Cade-Bray/Helgatchi/Hardware/Helgatchi front PCB/Components/801Logos/DC801.pdf

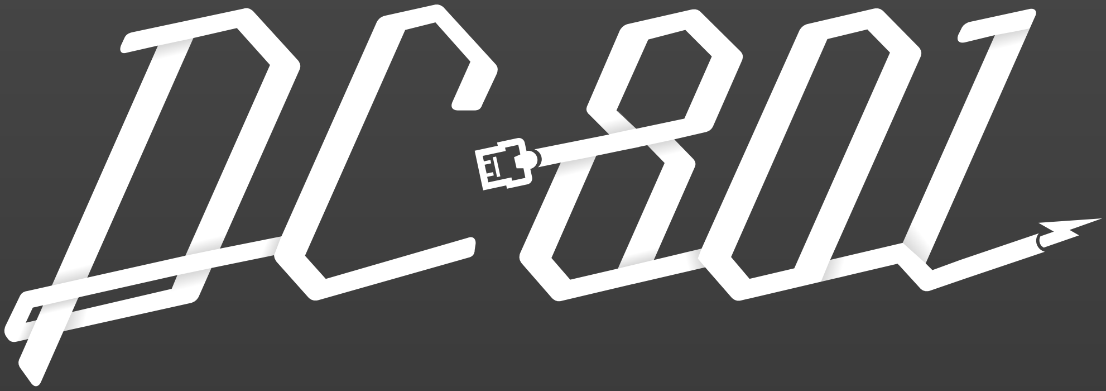
[picture p2: figure]
