Cade-Bray/Helgatchi/Hardware/Helgatchi front PCB/Components/801Logos/DC801_black.pdf

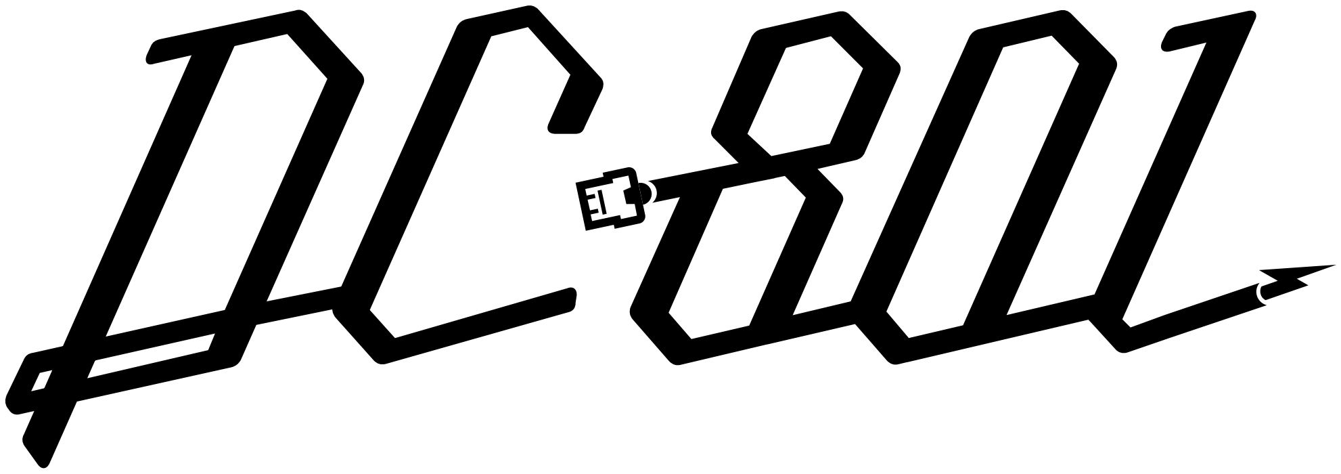
[picture p3: figure]
