Cade-Bray/Helgatchi/Hardware/Helgatchi front PCB/Components/801Logos/DC801_white.pdf

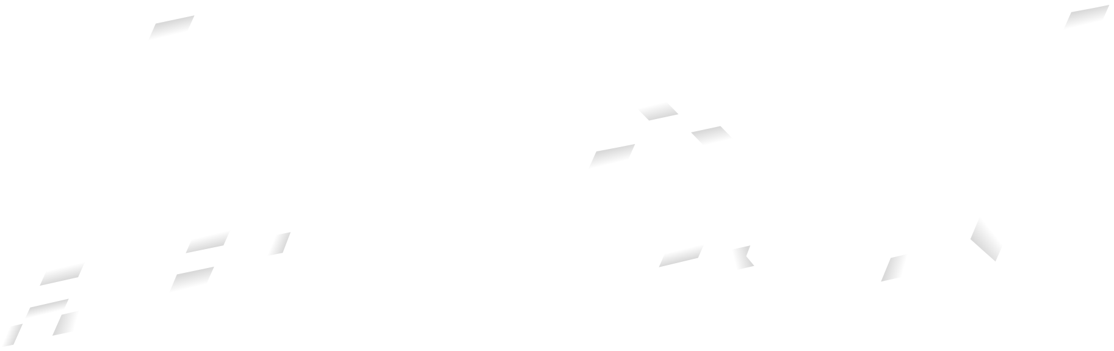
[picture p4: figure]
