Cade-Bray/Helgatchi/Hardware/Helgatchi Spacer/8.6mm Spacer antenna cutout 2.5mm holes.step

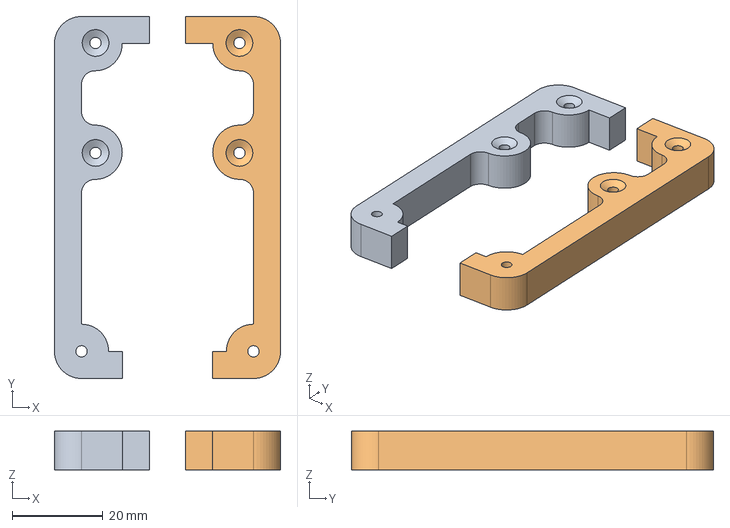
[picture p19: CAD file, 2026-04-04]
Hardware/Helgatchi Spacer/8.6mm Spacer antenna cutout 2.5mm holes.step
50.0 x 80.0 x 8.60 mm
