Cade-Bray/Helgatchi/Hardware/Helgatchi Spacer/Helgatchi Spacer - antenna - 2.5mm holes.dxf

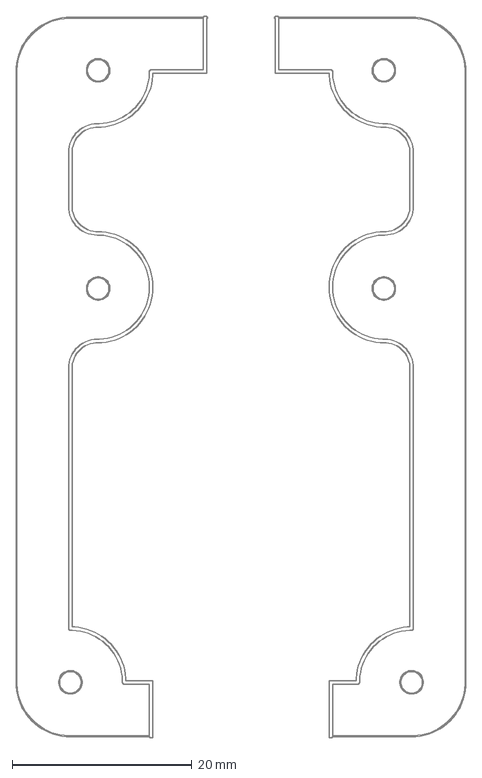
[picture p22: CAD file, 2026-04-04]
Hardware/Helgatchi Spacer/Helgatchi Spacer - antenna - 2.5mm holes.dxf
50.1 x 80.4 mm
