Cade-Bray/Helgatchi/Hardware/Helgatchi Spacer/Helgatchi spacer - antenna - 2.2mm holes.dxf

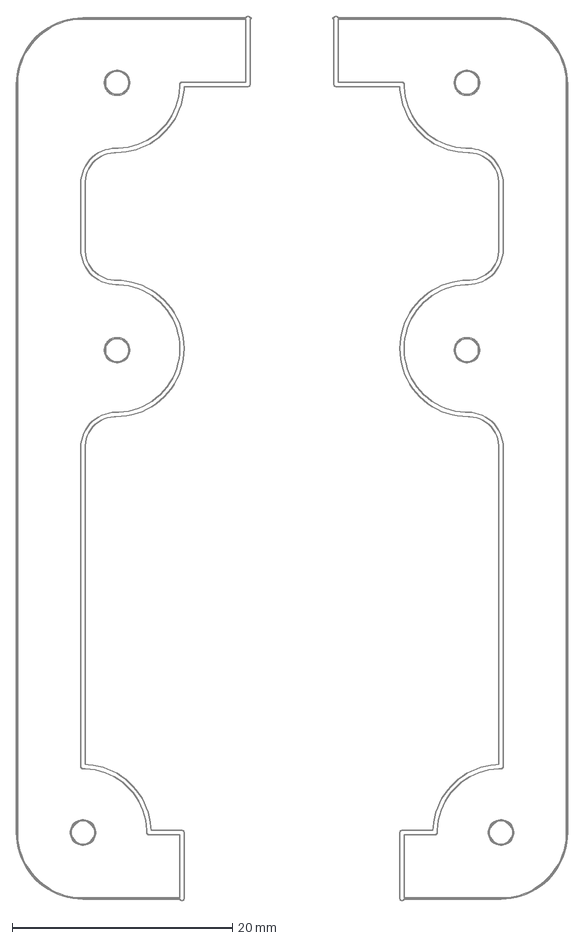
[picture p23: CAD file, 2026-04-04]
Hardware/Helgatchi Spacer/Helgatchi spacer - antenna - 2.2mm holes.dxf
50.1 x 80.4 mm
