Cade-Bray/Helgatchi/Hardware/Helgatchi Spacer/7.6mm Spacer.step

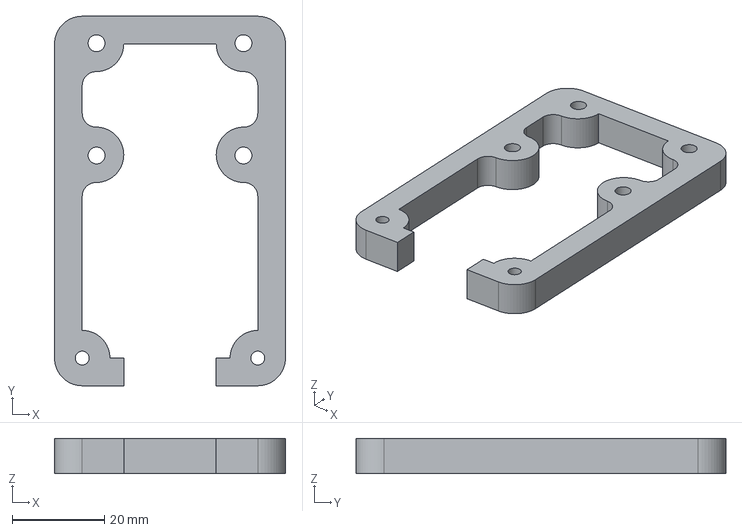
[picture p24: CAD file, 2026-03-17]
Hardware/Helgatchi Spacer/7.6mm Spacer.step
50.0 x 80.0 x 7.60 mm
