Cade-Bray/Helgatchi/Hardware/Helgatchi Spacer/8.6mm Spacer.step

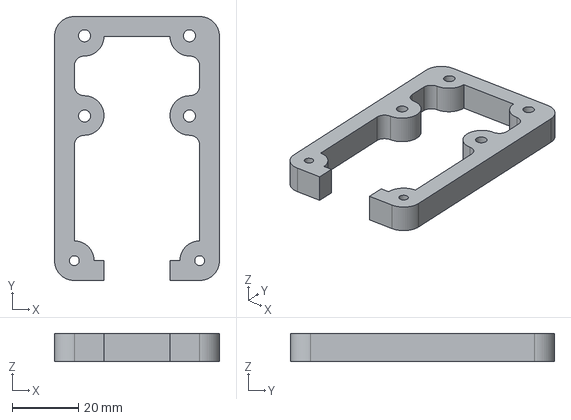
[picture p25: CAD file, 2026-03-17]
Hardware/Helgatchi Spacer/8.6mm Spacer.step
50.0 x 80.0 x 8.60 mm
