Cade-Bray/Helgatchi/Hardware/Helgatchi Spacer/Helgatchi back PCB-User_Drawings - unknown variant.dxf

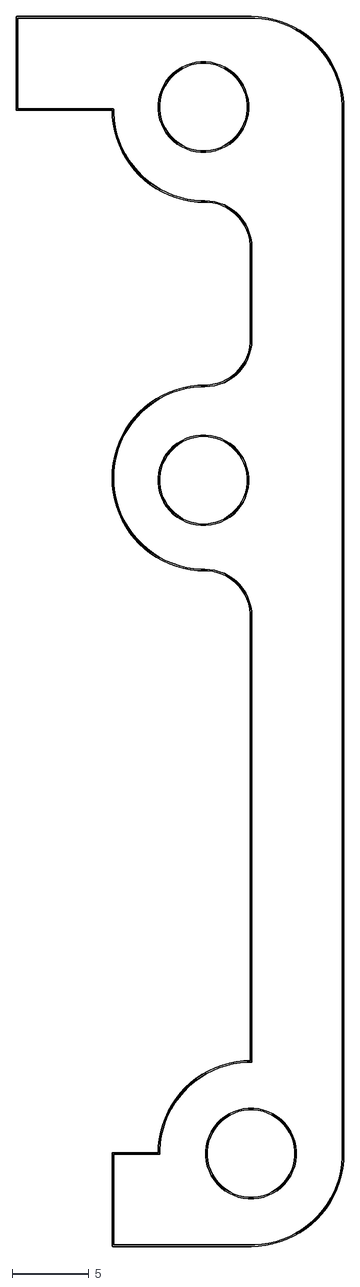
[picture p26: CAD file, 2026-02-06]
Hardware/Helgatchi Spacer/Helgatchi back PCB-User_Drawings - unknown variant.dxf
21.4 x 80.1
