Cade-Bray/Helgatchi/Hardware/Helgatchi Spacer/Helgatchi Spacer - antenna - standoffs.dxf

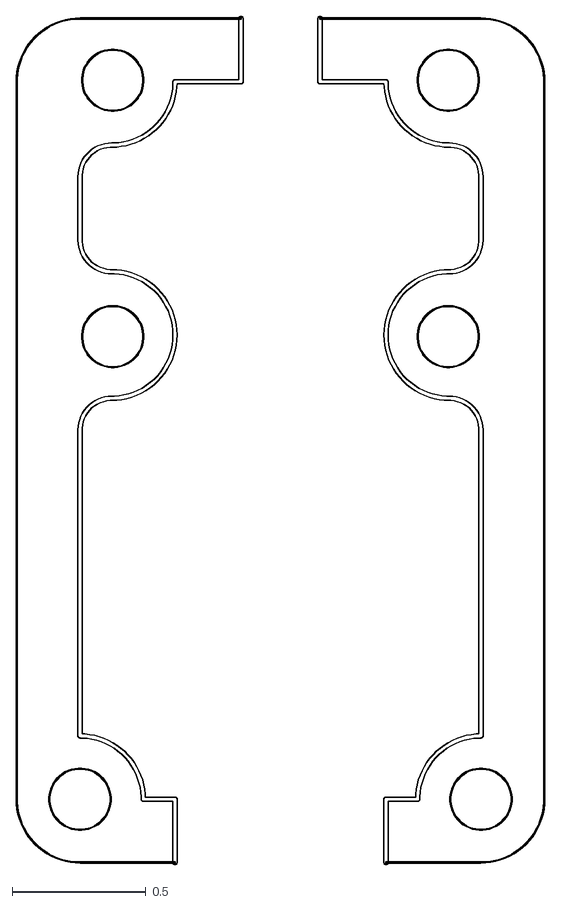
[picture p27: CAD file, 2026-02-05]
Hardware/Helgatchi Spacer/Helgatchi Spacer - antenna - standoffs.dxf
1.97 x 3.17
