Cade-Bray/Helgatchi/Hardware/Helgatchi Spacer/Helgatchi Spacer.dxf

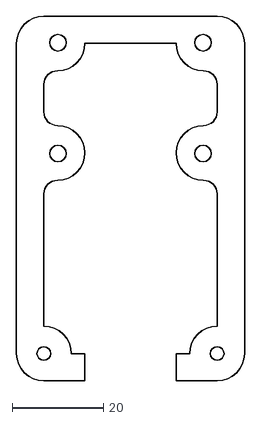
[picture p28: CAD file, 2026-01-26]
Hardware/Helgatchi Spacer/Helgatchi Spacer.dxf
50.0 x 80.0
