Cade-Bray/Helgatchi/Hardware/Helgatchi front PCB/Components/801Logos/801Labs_black.pdf

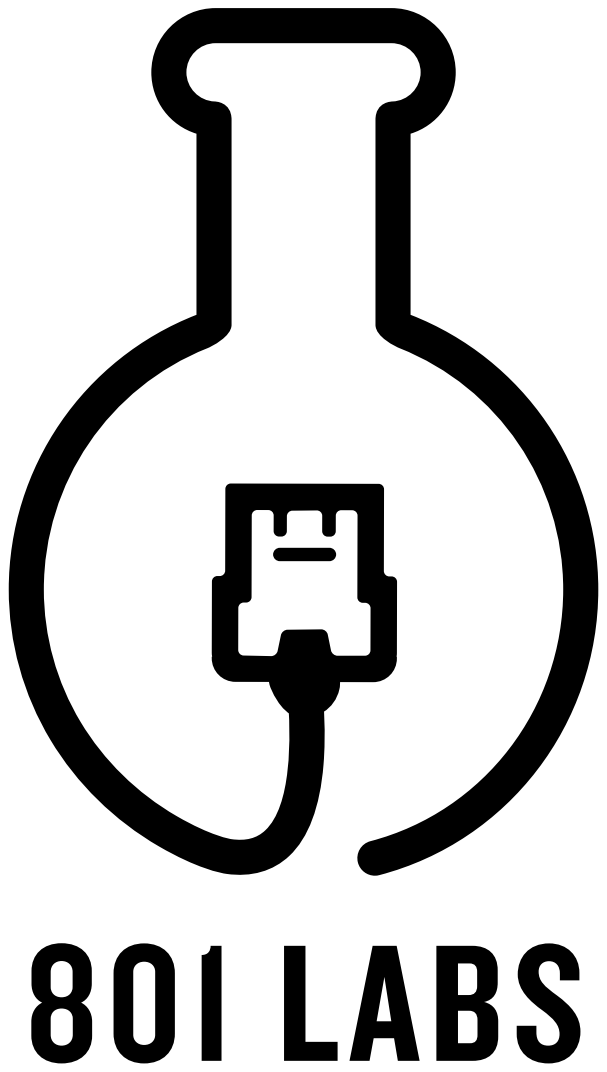
[picture p39: page 1]
