Cade-Bray/Helgatchi/Software/Helgatchi-Firmware/src/UI/ui.c

#include "ui.h"
#include "screens.h"
#include "images.h"
#include "actions.h"
#include "vars.h"

// ASSETS DEFINITION
const uint8_t assets[22956] = {
    0x7E, 0x45, 0x45, 0x5A, 0x03, 0x00, 0x06, 0x00, 0x00, 0x00, 0x00, 0x00, 0x24, 0x00, 0x00, 0x00,
    0x24, 0x00, 0x00, 0x00, 0x00, 0x00, 0x00, 0x00, 0x00, 0x00, 0x00, 0x00, 0x00, 0x00, 0x00, 0x00,
    0x00, 0x00, 0x00, 0x00, 0x20, 0x00, 0x00, 0x00, 0x00, 0x00, 0x00, 0x00, 0x00, 0x00, 0x00, 0x00,
    0x18, 0x01, 0xF0, 0x00, 0x03, 0x00, 0x00, 0x00, 0x24, 0x00, 0x00, 0x00, 0x02, 0x00, 0x00, 0x00,
    0x28, 0x00, 0x00, 0x00, 0x14, 0x00, 0x00, 0x00, 0x24, 0x00, 0x00, 0x00, 0x49, 0x00, 0x00, 0x00,
    0x70, 0x50, 0x00, 0x00, 0x02, 0x00, 0x00, 0x00, 0x64, 0x00, 0x00, 0x00, 0x68, 0x00, 0x00, 0x00,
    0x70, 0x00, 0x00, 0x00, 0x78, 0x00, 0x00, 0x00, 0x00, 0x00, 0xFF, 0xFF, 0x7C, 0x00, 0x00, 0x00,
    0xA8, 0x00, 0x00, 0x00, 0xD4, 0x00, 0x00, 0x00, 0x00, 0x01, 0x00, 0x00, 0x2C, 0x01, 0x00, 0x00,
    0x58, 0x01, 0x00, 0x00, 0x84, 0x01, 0x00, 0x00, 0xB0, 0x01, 0x00, 0x00, 0xDC, 0x01, 0x00, 0x00,
    0x08, 0x02, 0x00, 0x00, 0x34, 0x02, 0x00, 0x00, 0x60, 0x02, 0x00, 0x00, 0x8C, 0x02, 0x00, 0x00,
    0xB8, 0x02, 0x00, 0x00, 0xE4, 0x02, 0x00, 0x00, 0x10, 0x03, 0x00, 0x00, 0x3C, 0x03, 0x00, 0x00,
    0x68, 0x03, 0x00, 0x00, 0x94, 0x03, 0x00, 0x00, 0xC0, 0x03, 0x00, 0x00, 0xF0, 0x03, 0x00, 0x00,
    0xFC, 0x03, 0x00, 0x00, 0x08, 0x04, 0x00, 0x00, 0x06, 0x00, 0x00, 0x00, 0x08, 0x04, 0x00, 0x00,
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
    { NATIVE_VAR_TYPE_NONE, 0, 0 },
};

ActionExecFunc actions[] = {
    0
};

void ui_init() {
    eez_flow_init(assets, sizeof(assets), (lv_obj_t **)&objects, sizeof(objects), images, sizeof(images), actions);
}

void ui_tick() {
    eez_flow_tick();
    tick_screen(g_currentScreen);
}
