Cade-Bray/Helgatchi/Software/Helgatchi-Firmware/src/UI/screens.c

#include <string.h>

#include "screens.h"
#include "images.h"
#include "fonts.h"
#include "actions.h"
#include "vars.h"
#include "styles.h"
#include "ui.h"

#include <string.h>

objects_t objects;

static const char *screen_names[] = { "Main Menu", "Tutorial Splash Screen", "Tutorial", "Settings", "Info", "Screen Template", "Alerts", "Devices", "Device Updating", "Debug Info", "Overview", "Power Menu", "Power Action Screen", "Admin Menu", "Foxhunting Menu" };
static const char *object_names[] = { "main_menu", "tutorial_splash_screen", "tutorial", "settings", "info", "screen_template", "alerts", "devices", "device_updating", "debug_info", "overview", "power_menu", "power_action_screen", "admin_menu", "foxhunting_menu", "obj0", "obj0__top_bar", "obj0__left_text", "obj0__top_bar_center_text", "obj0__right_text", "settings_top_bar", "settings_top_bar__top_bar", "settings_top_bar__left_text", "settings_top_bar__top_bar_center_text", "settings_top_bar__right_text", "obj1", "obj1__top_bar", "obj1__left_text", "obj1__top_bar_center_text", "obj1__right_text", "obj2", "obj2__top_bar", "obj2__left_text", "obj2__top_bar_center_text", "obj2__right_text", "obj3", "obj3__main_content", "obj4", "obj4__top_bar", "obj4__left_text", "obj4__top_bar_center_text", "obj4__right_text", "obj5", "obj5__top_bar", "obj5__left_text", "obj5__top_bar_center_text", "obj5__right_text", "obj6", "obj6__top_bar", "obj6__left_text", "obj6__top_bar_center_text", "obj6__right_text", "obj7", "obj7__main_content", "obj8", "obj8__top_bar", "obj8__left_text", "obj8__top_bar_center_text", "obj8__right_text", "obj9", "obj9__top_bar", "obj9__left_text", "obj9__top_bar_center_text", "obj9__right_text", "obj10", "obj10__top_bar", "obj10__left_text", "obj10__top_bar_center_text", "obj10__right_text", "obj11", "obj11__top_bar", "obj11__left_text", "obj11__top_bar_center_text", "obj11__right_text", "obj12", "obj12__top_bar", "obj12__left_text", "obj12__top_bar_center_text", "obj12__right_text", "main_menu_scrolling_container", "overview_panel", "obj13", "devices_panel", "obj14", "alerts_panel", "games_panel", "settings_panel", "info_panel", "admin_panel", "obj15", "power_panel", "obj16", "obj17", "obj18", "obj19", "obj20", "splash_screen_tutorial", "obj21", "start_tutorial_button", "obj22", "obj23", "obj24", "end_tutorial_button", "obj25", "obj26", "obj27", "screen_brightness_dropdown", "led_brightness_dropdown", "vibrate_on_alert_switch", "le_ds_on_alert_switch", "wake_screen_on_alert_switch", "obj28", "focus_on_alert_page_switch", "ble_scanning_switch", "active_ble_scanning", "ignore_nameless_random_ma_cs", "wi_fi_scanning_switch", "scan_mode_dropdown", "debug_over_serial_switch", "debug_level_dropdown", "sleep_with_serial_switch", "sleep_with_usb_switch", "sleep_while_charging", "debug_screen_label", "debug_screen_button", "sleep_timer_label", "sleep_button", "reboot_button", "shipping_mode_button", "restart_tutorial_button", "obj29", "obj30", "obj31", "obj32", "obj33", "obj34", "obj35", "obj36", "obj37", "device_info", "version_info", "hardware_specs_container", "software_specs_container", "credits_container", "obj38", "alert_container", "no_alerts_label", "devices_container", "obj39", "system___health_container", "power_container", "scanning_container", "rules___alerts_container", "helga", "sleep_now_button", "sleep_countdown_text", "restart_button", "power_off_", "obj40", "obj41", "obj42", "power_action_text", "admin_command_container", "admin_command_dropdown", "admin_message_container", "admin_message_dropdown", "admin_led_pattern_container", "admin_led_mode_dropdown", "admin_duration_container", "admin_duration_dropdown", "admin_command_button", "admin_command_button_label", "signal_quality", "device_name", "last_seen", "device_rssi", "device_details", "obj43", "obj44", "obj45", "obj46", "obj47", "obj48", "obj49", "obj50", "obj51", "obj52", "obj53", "obj54", "obj55" };

//
// Event handlers
//

lv_obj_t *tick_value_change_obj;

static void event_handler_cb_main_menu_main_menu(lv_event_t *e) {
    lv_event_code_t event = lv_event_get_code(e);
    void *flowState = lv_event_get_user_data(e);
    (void)flowState;
    
    if (event == LV_EVENT_SCREEN_LOAD_START) {
        // group: UINavigation
        lv_group_remove_all_objs(groups.UINavigation);
        lv_group_add_obj(groups.UINavigation, objects.overview_panel);
        lv_group_add_obj(groups.UINavigation, objects.devices_panel);
        lv_group_add_obj(groups.UINavigation, objects.alerts_panel);
        lv_group_add_obj(groups.UINavigation, objects.games_panel);
        lv_group_add_obj(groups.UINavigation, objects.settings_panel);
        lv_group_add_obj(groups.UINavigation, objects.info_panel);
        lv_group_add_obj(groups.UINavigation, objects.admin_panel);
        lv_group_add_obj(groups.UINavigation, objects.power_panel);
    }
    if (event == LV_EVENT_SCREEN_LOADED) {
        e->user_data = (void *)0;
        flowPropagateValueLVGLEvent(flowState, 1, 0, e);
    }
}

static void event_handler_cb_main_menu_overview_panel(lv_event_t *e) {
    lv_event_code_t event = lv_event_get_code(e);
    void *flowState = lv_event_get_user_data(e);
    (void)flowState;
    
    if (event == LV_EVENT_CLICKED) {
        e->user_data = (void *)0;
        flowPropagateValueLVGLEvent(flowState, 3, 0, e);
    }
}

static void event_handler_cb_main_menu_devices_panel(lv_event_t *e) {
    lv_event_code_t event = lv_event_get_code(e);
    void *flowState = lv_event_get_user_data(e);
    (void)flowState;
    
    if (event == LV_EVENT_CLICKED) {
        e->user_data = (void *)0;
        flowPropagateValueLVGLEvent(flowState, 7, 0, e);
    }
}

static void event_handler_cb_main_menu_alerts_panel(lv_event_t *e) {
    lv_event_code_t event = lv_event_get_code(e);
    void *flowState = lv_event_get_user_data(e);
    (void)flowState;
    
    if (event == LV_EVENT_CLICKED) {
        e->user_data = (void *)0;
        flowPropagateValueLVGLEvent(flowState, 11, 0, e);
    }
}

static void event_handler_cb_main_menu_games_panel(lv_event_t *e) {
    lv_event_code_t event = lv_event_get_code(e);
    void *flowState = lv_event_get_user_data(e);
    (void)flowState;
    
    if (event == LV_EVENT_CLICKED) {
        e->user_data = (void *)0;
        flowPropagateValueLVGLEvent(flowState, 15, 0, e);
    }
}

static void event_handler_cb_main_menu_settings_panel(lv_event_t *e) {
    lv_event_code_t event = lv_event_get_code(e);
    void *flowState = lv_event_get_user_data(e);
    (void)flowState;
    
    if (event == LV_EVENT_CLICKED) {
        e->user_data = (void *)0;
        flowPropagateValueLVGLEvent(flowState, 19, 0, e);
    }
}

static void event_handler_cb_main_menu_info_panel(lv_event_t *e) {
    lv_event_code_t event = lv_event_get_code(e);
    void *flowState = lv_event_get_user_data(e);
    (void)flowState;
    
    if (event == LV_EVENT_CLICKED) {
        e->user_data = (void *)0;
        flowPropagateValueLVGLEvent(flowState, 23, 0, e);
    }
}

static void event_handler_cb_main_menu_admin_panel(lv_event_t *e) {
    lv_event_code_t event = lv_event_get_code(e);
    void *flowState = lv_event_get_user_data(e);
    (void)flowState;
    
    if (event == LV_EVENT_CLICKED) {
        e->user_data = (void *)0;
        flowPropagateValueLVGLEvent(flowState, 27, 0, e);
    }
}

static void event_handler_cb_main_menu_power_panel(lv_event_t *e) {
    lv_event_code_t event = lv_event_get_code(e);
    void *flowState = lv_event_get_user_data(e);
    (void)flowState;
    
    if (event == LV_EVENT_CLICKED) {
        e->user_data = (void *)0;
        flowPropagateValueLVGLEvent(flowState, 31, 0, e);
    }
}

static void event_handler_cb_tutorial_splash_screen_tutorial_splash_screen(lv_event_t *e) {
    lv_event_code_t event = lv_event_get_code(e);
    void *flowState = lv_event_get_user_data(e);
    (void)flowState;
    
    if (event == LV_EVENT_SCREEN_LOAD_START) {
        // group: UINavigation
        lv_group_remove_all_objs(groups.UINavigation);
        lv_group_add_obj(groups.UINavigation, objects.start_tutorial_button);
    }
}

static void event_handler_cb_tutorial_splash_screen_start_tutorial_button(lv_event_t *e) {
    lv_event_code_t event = lv_event_get_code(e);
    void *flowState = lv_event_get_user_data(e);
    (void)flowState;
    
    if (event == LV_EVENT_CLICKED) {
        e->user_data = (void *)0;
        flowPropagateValueLVGLEvent(flowState, 4, 0, e);
    }
}

static void event_handler_cb_tutorial_tutorial(lv_event_t *e) {
    lv_event_code_t event = lv_event_get_code(e);
    void *flowState = lv_event_get_user_data(e);
    (void)flowState;
    
    if (event == LV_EVENT_SCREEN_LOAD_START) {
        // group: UINavigation
        lv_group_remove_all_objs(groups.UINavigation);
        lv_group_add_obj(groups.UINavigation, objects.obj43);
        lv_group_add_obj(groups.UINavigation, objects.obj44);
        lv_group_add_obj(groups.UINavigation, objects.obj45);
        lv_group_add_obj(groups.UINavigation, objects.obj46);
        lv_group_add_obj(groups.UINavigation, objects.obj47);
        lv_group_add_obj(groups.UINavigation, objects.end_tutorial_button);
    }
    if (event == LV_EVENT_SCREEN_LOADED) {
        e->user_data = (void *)0;
        flowPropagateValueLVGLEvent(flowState, 1, 0, e);
    }
    if (event == LV_EVENT_SCREEN_UNLOADED) {
        e->user_data = (void *)0;
        flowPropagateValueLVGLEvent(flowState, 1, 1, e);
    }
}

static void event_handler_cb_tutorial_end_tutorial_button(lv_event_t *e) {
    lv_event_code_t event = lv_event_get_code(e);
    void *flowState = lv_event_get_user_data(e);
    (void)flowState;
    
    if (event == LV_EVENT_CLICKED) {
        e->user_data = (void *)0;
        flowPropagateValueLVGLEvent(flowState, 21, 0, e);
    }
}

static void event_handler_cb_settings_settings(lv_event_t *e) {
    lv_event_code_t event = lv_event_get_code(e);
    void *flowState = lv_event_get_user_data(e);
    (void)flowState;
    
    if (event == LV_EVENT_SCREEN_LOAD_START) {
        // group: UINavigation
        lv_group_remove_all_objs(groups.UINavigation);
        lv_group_add_obj(groups.UINavigation, objects.screen_brightness_dropdown);
        lv_group_add_obj(groups.UINavigation, objects.led_brightness_dropdown);
        lv_group_add_obj(groups.UINavigation, objects.vibrate_on_alert_switch);
        lv_group_add_obj(groups.UINavigation, objects.le_ds_on_alert_switch);
        lv_group_add_obj(groups.UINavigation, objects.wake_screen_on_alert_switch);
        lv_group_add_obj(groups.UINavigation, objects.focus_on_alert_page_switch);
        lv_group_add_obj(groups.UINavigation, objects.ble_scanning_switch);
        lv_group_add_obj(groups.UINavigation, objects.active_ble_scanning);
        lv_group_add_obj(groups.UINavigation, objects.ignore_nameless_random_ma_cs);
        lv_group_add_obj(groups.UINavigation, objects.wi_fi_scanning_switch);
        lv_group_add_obj(groups.UINavigation, objects.scan_mode_dropdown);
        lv_group_add_obj(groups.UINavigation, objects.debug_over_serial_switch);
        lv_group_add_obj(groups.UINavigation, objects.debug_level_dropdown);
        lv_group_add_obj(groups.UINavigation, objects.sleep_with_serial_switch);
        lv_group_add_obj(groups.UINavigation, objects.sleep_with_usb_switch);
        lv_group_add_obj(groups.UINavigation, objects.sleep_while_charging);
        lv_group_add_obj(groups.UINavigation, objects.debug_screen_button);
        lv_group_add_obj(groups.UINavigation, objects.sleep_button);
        lv_group_add_obj(groups.UINavigation, objects.reboot_button);
        lv_group_add_obj(groups.UINavigation, objects.shipping_mode_button);
        lv_group_add_obj(groups.UINavigation, objects.restart_tutorial_button);
    }
}

static void event_handler_cb_settings_wake_screen_on_alert_switch(lv_event_t *e) {
    lv_event_code_t event = lv_event_get_code(e);
    void *flowState = lv_event_get_user_data(e);
    (void)flowState;
    
    if (event == LV_EVENT_VALUE_CHANGED) {
        if (!lv_obj_has_state(lv_event_get_target_obj(e), LV_STATE_CHECKED)) {
            e->user_data = (void *)0;
            flowPropagateValueLVGLEvent(flowState, 19, 0, e);
        }
    }
    if (event == LV_EVENT_VALUE_CHANGED) {
        if (lv_obj_has_state(lv_event_get_target_obj(e), LV_STATE_CHECKED)) {
            e->user_data = (void *)0;
            flowPropagateValueLVGLEvent(flowState, 19, 1, e);
        }
    }
}

static void event_handler_cb_settings_debug_screen_button(lv_event_t *e) {
    lv_event_code_t event = lv_event_get_code(e);
    void *flowState = lv_event_get_user_data(e);
    (void)flowState;
    
    if (event == LV_EVENT_CLICKED) {
        e->user_data = (void *)0;
        flowPropagateValueLVGLEvent(flowState, 57, 0, e);
    }
}

static void event_handler_cb_settings_restart_tutorial_button(lv_event_t *e) {
    lv_event_code_t event = lv_event_get_code(e);
    void *flowState = lv_event_get_user_data(e);
    (void)flowState;
    
    if (event == LV_EVENT_CLICKED) {
        e->user_data = (void *)0;
        flowPropagateValueLVGLEvent(flowState, 73, 0, e);
    }
}

static void event_handler_cb_info_info(lv_event_t *e) {
    lv_event_code_t event = lv_event_get_code(e);
    void *flowState = lv_event_get_user_data(e);
    (void)flowState;
    
    if (event == LV_EVENT_SCREEN_LOAD_START) {
        // group: UINavigation
        lv_group_remove_all_objs(groups.UINavigation);
        lv_group_add_obj(groups.UINavigation, objects.obj48);
        lv_group_add_obj(groups.UINavigation, objects.obj49);
        lv_group_add_obj(groups.UINavigation, objects.obj50);
        lv_group_add_obj(groups.UINavigation, objects.obj51);
    }
}

static void event_handler_cb_screen_template_screen_template(lv_event_t *e) {
    lv_event_code_t event = lv_event_get_code(e);
    void *flowState = lv_event_get_user_data(e);
    (void)flowState;
    
    if (event == LV_EVENT_SCREEN_LOAD_START) {
        // group: UINavigation
        lv_group_remove_all_objs(groups.UINavigation);
    }
}

static void event_handler_cb_alerts_alerts(lv_event_t *e) {
    lv_event_code_t event = lv_event_get_code(e);
    void *flowState = lv_event_get_user_data(e);
    (void)flowState;
    
    if (event == LV_EVENT_SCREEN_LOAD_START) {
        // group: UINavigation
        lv_group_remove_all_objs(groups.UINavigation);
    }
}

static void event_handler_cb_devices_devices(lv_event_t *e) {
    lv_event_code_t event = lv_event_get_code(e);
    void *flowState = lv_event_get_user_data(e);
    (void)flowState;
    
    if (event == LV_EVENT_SCREEN_LOAD_START) {
        // group: UINavigation
        lv_group_remove_all_objs(groups.UINavigation);
    }
}

static void event_handler_cb_device_updating_device_updating(lv_event_t *e) {
    lv_event_code_t event = lv_event_get_code(e);
    void *flowState = lv_event_get_user_data(e);
    (void)flowState;
    
    if (event == LV_EVENT_SCREEN_LOAD_START) {
        // group: UINavigation
        lv_group_remove_all_objs(groups.UINavigation);
    }
}

static void event_handler_cb_debug_info_debug_info(lv_event_t *e) {
    lv_event_code_t event = lv_event_get_code(e);
    void *flowState = lv_event_get_user_data(e);
    (void)flowState;
    
    if (event == LV_EVENT_SCREEN_LOAD_START) {
        // group: UINavigation
        lv_group_remove_all_objs(groups.UINavigation);
        lv_group_add_obj(groups.UINavigation, objects.obj52);
        lv_group_add_obj(groups.UINavigation, objects.obj53);
        lv_group_add_obj(groups.UINavigation, objects.obj54);
        lv_group_add_obj(groups.UINavigation, objects.obj55);
    }
}

static void event_handler_cb_overview_overview(lv_event_t *e) {
    lv_event_code_t event = lv_event_get_code(e);
    void *flowState = lv_event_get_user_data(e);
    (void)flowState;
    
    if (event == LV_EVENT_SCREEN_LOAD_START) {
        // group: UINavigation
        lv_group_remove_all_objs(groups.UINavigation);
    }
}

static void event_handler_cb_power_menu_power_menu(lv_event_t *e) {
    lv_event_code_t event = lv_event_get_code(e);
    void *flowState = lv_event_get_user_data(e);
    (void)flowState;
    
    if (event == LV_EVENT_SCREEN_LOAD_START) {
        // group: UINavigation
        lv_group_remove_all_objs(groups.UINavigation);
        lv_group_add_obj(groups.UINavigation, objects.sleep_now_button);
        lv_group_add_obj(groups.UINavigation, objects.restart_button);
        lv_group_add_obj(groups.UINavigation, objects.power_off_);
    }
}

static void event_handler_cb_power_action_screen_power_action_screen(lv_event_t *e) {
    lv_event_code_t event = lv_event_get_code(e);
    void *flowState = lv_event_get_user_data(e);
    (void)flowState;
    
    if (event == LV_EVENT_SCREEN_LOAD_START) {
        // group: UINavigation
        lv_group_remove_all_objs(groups.UINavigation);
    }
}

static void event_handler_cb_admin_menu_admin_menu(lv_event_t *e) {
    lv_event_code_t event = lv_event_get_code(e);
    void *flowState = lv_event_get_user_data(e);
    (void)flowState;
    
    if (event == LV_EVENT_SCREEN_LOAD_START) {
        // group: UINavigation
        lv_group_remove_all_objs(groups.UINavigation);
        lv_group_add_obj(groups.UINavigation, objects.admin_command_dropdown);
        lv_group_add_obj(groups.UINavigation, objects.admin_message_dropdown);
        lv_group_add_obj(groups.UINavigation, objects.admin_led_mode_dropdown);
        lv_group_add_obj(groups.UINavigation, objects.admin_duration_dropdown);
    }
}

static void event_handler_cb_foxhunting_menu_foxhunting_menu(lv_event_t *e) {
    lv_event_code_t event = lv_event_get_code(e);
    void *flowState = lv_event_get_user_data(e);
    (void)flowState;
    
    if (event == LV_EVENT_SCREEN_LOAD_START) {
        // group: UINavigation
        lv_group_remove_all_objs(groups.UINavigation);
    }
}

//
// Screens
//

void create_screen_main_menu() {
    void *flowState = getFlowState(0, 0);
    (void)flowState;
    lv_obj_t *obj = lv_obj_create(0);
    objects.main_menu = obj;
    lv_obj_set_pos(obj, 0, 0);
    lv_obj_set_size(obj, 280, 240);
    lv_obj_add_event_cb(obj, event_handler_cb_main_menu_main_menu, LV_EVENT_ALL, flowState);
    {
        lv_obj_t *parent_obj = obj;
        {
            lv_obj_t *obj = lv_obj_create(parent_obj);
            objects.obj0 = obj;
            lv_obj_set_pos(obj, 0, 0);
            lv_obj_set_size(obj, 280, 36);
            lv_obj_set_style_pad_left(obj, 0, LV_PART_MAIN | LV_STATE_DEFAULT);
            lv_obj_set_style_pad_top(obj, 0, LV_PART_MAIN | LV_STATE_DEFAULT);
            lv_obj_set_style_pad_right(obj, 0, LV_PART_MAIN | LV_STATE_DEFAULT);
            lv_obj_set_style_pad_bottom(obj, 0, LV_PART_MAIN | LV_STATE_DEFAULT);
            lv_obj_set_style_bg_opa(obj, 0, LV_PART_MAIN | LV_STATE_DEFAULT);
            lv_obj_set_style_border_width(obj, 0, LV_PART_MAIN | LV_STATE_DEFAULT);
            create_user_widget_top_bar(obj, getFlowState(flowState, 0), 16);
            lv_obj_add_flag(obj, LV_OBJ_FLAG_FLOATING);
        }
        {
            // Main Menu Scrolling Container
            lv_obj_t *obj = lv_obj_create(parent_obj);
            objects.main_menu_scrolling_container = obj;
            lv_obj_set_pos(obj, 0, 0);
            lv_obj_set_size(obj, LV_PCT(100), LV_PCT(85));
            lv_obj_set_style_pad_left(obj, 0, LV_PART_MAIN | LV_STATE_DEFAULT);
            lv_obj_set_style_pad_top(obj, 0, LV_PART_MAIN | LV_STATE_DEFAULT);
            lv_obj_set_style_pad_right(obj, 0, LV_PART_MAIN | LV_STATE_DEFAULT);
            lv_obj_set_style_pad_bottom(obj, 0, LV_PART_MAIN | LV_STATE_DEFAULT);
            lv_obj_set_style_bg_opa(obj, 0, LV_PART_MAIN | LV_STATE_DEFAULT);
            lv_obj_set_style_border_width(obj, 0, LV_PART_MAIN | LV_STATE_DEFAULT);
            lv_obj_set_style_radius(obj, 0, LV_PART_MAIN | LV_STATE_DEFAULT);
            lv_obj_add_flag(obj, LV_OBJ_FLAG_SCROLL_ON_FOCUS|LV_OBJ_FLAG_SCROLL_ONE);
            lv_obj_remove_flag(obj, LV_OBJ_FLAG_CLICKABLE|LV_OBJ_FLAG_SCROLL_MOMENTUM);
            lv_obj_set_scrollbar_mode(obj, LV_SCROLLBAR_MODE_ON);
            lv_obj_set_scroll_dir(obj, LV_DIR_HOR);
            lv_obj_set_scroll_snap_x(obj, LV_SCROLL_SNAP_CENTER);
            lv_obj_set_style_align(obj, LV_ALIGN_BOTTOM_MID, LV_PART_MAIN | LV_STATE_DEFAULT);
            lv_obj_set_style_layout(obj, LV_LAYOUT_FLEX, LV_PART_MAIN | LV_STATE_DEFAULT);
            lv_obj_set_style_flex_flow(obj, LV_FLEX_FLOW_COLUMN_WRAP, LV_PART_MAIN | LV_STATE_DEFAULT);
            {
                lv_obj_t *parent_obj = obj;
                {
                    // Overview Panel
                    lv_obj_t *obj = lv_obj_create(parent_obj);
                    objects.overview_panel = obj;
                    lv_obj_set_pos(obj, 14, 28);
                    lv_obj_set_size(obj, LV_PCT(100), LV_PCT(100));
                    lv_obj_add_event_cb(obj, event_handler_cb_main_menu_overview_panel, LV_EVENT_ALL, flowState);
                    lv_obj_add_flag(obj, LV_OBJ_FLAG_SCROLL_ON_FOCUS);
                    lv_obj_add_state(obj, LV_STATE_FOCUS_KEY);
                    add_style_default_main_menu_panel(obj);
                    {
                        lv_obj_t *parent_obj = obj;
                        {
                            lv_obj_t *obj = lv_label_create(parent_obj);
                            objects.obj13 = obj;
                            lv_obj_set_pos(obj, 0, 0);
                            lv_obj_set_size(obj, LV_SIZE_CONTENT, LV_SIZE_CONTENT);
                            lv_obj_set_style_text_font(obj, &lv_font_montserrat_44, LV_PART_MAIN | LV_STATE_DEFAULT);
                            lv_obj_set_style_text_color(obj, lv_color_hex(0xfafafa), LV_PART_MAIN | LV_STATE_DEFAULT);
                            lv_label_set_text(obj, "");
                        }
                        {
                            lv_obj_t *obj = lv_label_create(parent_obj);
                            lv_obj_set_pos(obj, 0, 0);
                            lv_obj_set_size(obj, LV_SIZE_CONTENT, LV_SIZE_CONTENT);
                            lv_obj_set_style_text_font(obj, &lv_font_montserrat_22, LV_PART_MAIN | LV_STATE_DEFAULT);
                            lv_label_set_text(obj, _("Status"));
                        }
                        {
                            lv_obj_t *obj = lv_label_create(parent_obj);
                            lv_obj_set_pos(obj, 0, 0);
                            lv_obj_set_size(obj, LV_PCT(90), LV_SIZE_CONTENT);
                            lv_obj_set_style_text_align(obj, LV_TEXT_ALIGN_CENTER, LV_PART_MAIN | LV_STATE_DEFAULT);
                            lv_label_set_text_static(obj, "Helga will show you what she's doing!");
                        }
                    }
                }
                {
                    // Devices Panel
                    lv_obj_t *obj = lv_obj_create(parent_obj);
                    objects.devices_panel = obj;
                    lv_obj_set_pos(obj, 14, 28);
                    lv_obj_set_size(obj, LV_PCT(100), LV_PCT(100));
                    lv_obj_add_event_cb(obj, event_handler_cb_main_menu_devices_panel, LV_EVENT_ALL, flowState);
                    lv_obj_add_flag(obj, LV_OBJ_FLAG_SCROLL_ON_FOCUS);
                    lv_obj_add_state(obj, LV_STATE_FOCUS_KEY);
                    add_style_default_main_menu_panel(obj);
                    {
                        lv_obj_t *parent_obj = obj;
                        {
                            lv_obj_t *obj = lv_label_create(parent_obj);
                            objects.obj14 = obj;
                            lv_obj_set_pos(obj, 0, 0);
                            lv_obj_set_size(obj, LV_SIZE_CONTENT, LV_SIZE_CONTENT);
                            lv_obj_set_style_text_font(obj, &lv_font_montserrat_44, LV_PART_MAIN | LV_STATE_DEFAULT);
                            lv_obj_set_style_text_color(obj, lv_color_hex(0xfafafa), LV_PART_MAIN | LV_STATE_DEFAULT);
                            lv_label_set_text(obj, "");
                        }
                        {
                            lv_obj_t *obj = lv_label_create(parent_obj);
                            lv_obj_set_pos(obj, 0, 0);
                            lv_obj_set_size(obj, LV_SIZE_CONTENT, LV_SIZE_CONTENT);
                            lv_obj_set_style_text_font(obj, &lv_font_montserrat_22, LV_PART_MAIN | LV_STATE_DEFAULT);
                            lv_label_set_text(obj, _("Devices"));
                        }
                        {
                            lv_obj_t *obj = lv_label_create(parent_obj);
                            lv_obj_set_pos(obj, 0, 0);
                            lv_obj_set_size(obj, LV_SIZE_CONTENT, LV_SIZE_CONTENT);
                            lv_label_set_text_static(obj, "View scan results!");
                        }
                    }
                }
                {
                    // Alerts Panel
                    lv_obj_t *obj = lv_obj_create(parent_obj);
                    objects.alerts_panel = obj;
                    lv_obj_set_pos(obj, 14, 28);
                    lv_obj_set_size(obj, LV_PCT(100), LV_PCT(100));
                    lv_obj_add_event_cb(obj, event_handler_cb_main_menu_alerts_panel, LV_EVENT_ALL, flowState);
                    lv_obj_add_flag(obj, LV_OBJ_FLAG_SCROLL_ON_FOCUS);
                    add_style_default_main_menu_panel(obj);
                    {
                        lv_obj_t *parent_obj = obj;
                        {
                            lv_obj_t *obj = lv_label_create(parent_obj);
                            objects.obj16 = obj;
                            lv_obj_set_pos(obj, 0, 0);
                            lv_obj_set_size(obj, LV_SIZE_CONTENT, LV_SIZE_CONTENT);
                            lv_obj_set_style_text_font(obj, &lv_font_montserrat_44, LV_PART_MAIN | LV_STATE_DEFAULT);
                            lv_label_set_text(obj, "");
                        }
                        {
                            lv_obj_t *obj = lv_label_create(parent_obj);
                            lv_obj_set_pos(obj, 0, 0);
                            lv_obj_set_size(obj, LV_SIZE_CONTENT, LV_SIZE_CONTENT);
                            lv_obj_set_style_text_font(obj, &lv_font_montserrat_22, LV_PART_MAIN | LV_STATE_DEFAULT);
                            lv_label_set_text(obj, _("Alerts"));
                        }
                        {
                            lv_obj_t *obj = lv_label_create(parent_obj);
                            lv_obj_set_pos(obj, 0, 0);
                            lv_obj_set_size(obj, LV_SIZE_CONTENT, LV_SIZE_CONTENT);
                            lv_label_set_text_static(obj, "Review alerts from Helgatchi!");
                        }
                    }
                }
                {
                    // Games Panel
                    lv_obj_t *obj = lv_obj_create(parent_obj);
                    objects.games_panel = obj;
                    lv_obj_set_pos(obj, 14, 28);
                    lv_obj_set_size(obj, LV_PCT(100), LV_PCT(100));
                    lv_obj_add_event_cb(obj, event_handler_cb_main_menu_games_panel, LV_EVENT_ALL, flowState);
                    lv_obj_add_flag(obj, LV_OBJ_FLAG_SCROLL_ON_FOCUS|LV_OBJ_FLAG_HIDDEN);
                    add_style_default_main_menu_panel(obj);
                    {
                        lv_obj_t *parent_obj = obj;
                        {
                            lv_obj_t *obj = lv_label_create(parent_obj);
                            objects.obj17 = obj;
                            lv_obj_set_pos(obj, 0, 0);
                            lv_obj_set_size(obj, LV_SIZE_CONTENT, LV_SIZE_CONTENT);
                            lv_obj_set_style_text_font(obj, &lv_font_montserrat_44, LV_PART_MAIN | LV_STATE_DEFAULT);
                            lv_label_set_text(obj, "");
                        }
                        {
                            lv_obj_t *obj = lv_label_create(parent_obj);
                            lv_obj_set_pos(obj, 0, 0);
                            lv_obj_set_size(obj, LV_SIZE_CONTENT, LV_SIZE_CONTENT);
                            lv_obj_set_style_text_font(obj, &lv_font_montserrat_22, LV_PART_MAIN | LV_STATE_DEFAULT);
                            lv_label_set_text(obj, _("Games"));
                        }
                        {
                            lv_obj_t *obj = lv_label_create(parent_obj);
                            lv_obj_set_pos(obj, 0, 0);
                            lv_obj_set_size(obj, LV_SIZE_CONTENT, LV_SIZE_CONTENT);
                            lv_label_set_text_static(obj, "Play cute minigames with Helga!");
                        }
                    }
                }
                {
                    // Settings Panel
                    lv_obj_t *obj = lv_obj_create(parent_obj);
                    objects.settings_panel = obj;
                    lv_obj_set_pos(obj, 0, 0);
                    lv_obj_set_size(obj, LV_PCT(100), LV_PCT(100));
                    lv_obj_add_event_cb(obj, event_handler_cb_main_menu_settings_panel, LV_EVENT_ALL, flowState);
                    lv_obj_add_flag(obj, LV_OBJ_FLAG_SCROLL_ON_FOCUS);
                    add_style_default_main_menu_panel(obj);
                    {
                        lv_obj_t *parent_obj = obj;
                        {
                            lv_obj_t *obj = lv_label_create(parent_obj);
                            objects.obj18 = obj;
                            lv_obj_set_pos(obj, 0, 0);
                            lv_obj_set_size(obj, LV_SIZE_CONTENT, LV_SIZE_CONTENT);
                            lv_obj_set_style_text_font(obj, &lv_font_montserrat_44, LV_PART_MAIN | LV_STATE_DEFAULT);
                            lv_label_set_text(obj, "");
                        }
                        {
                            lv_obj_t *obj = lv_label_create(parent_obj);
                            lv_obj_set_pos(obj, 0, 0);
                            lv_obj_set_size(obj, LV_SIZE_CONTENT, LV_SIZE_CONTENT);
                            lv_obj_set_style_text_font(obj, &lv_font_montserrat_22, LV_PART_MAIN | LV_STATE_DEFAULT);
                            lv_label_set_text(obj, _("Settings"));
                        }
                        {
                            lv_obj_t *obj = lv_label_create(parent_obj);
                            lv_obj_set_pos(obj, 0, 0);
                            lv_obj_set_size(obj, LV_SIZE_CONTENT, LV_SIZE_CONTENT);
                            lv_label_set_text_static(obj, "Customize your Helgatchi!");
                        }
                    }
                }
                {
                    // Info Panel
                    lv_obj_t *obj = lv_obj_create(parent_obj);
                    objects.info_panel = obj;
                    lv_obj_set_pos(obj, 14, 28);
                    lv_obj_set_size(obj, LV_PCT(100), LV_PCT(100));
                    lv_obj_add_event_cb(obj, event_handler_cb_main_menu_info_panel, LV_EVENT_ALL, flowState);
                    lv_obj_add_flag(obj, LV_OBJ_FLAG_SCROLL_ON_FOCUS);
                    add_style_default_main_menu_panel(obj);
                    {
                        lv_obj_t *parent_obj = obj;
                        {
                            lv_obj_t *obj = lv_label_create(parent_obj);
                            objects.obj19 = obj;
                            lv_obj_set_pos(obj, 0, 0);
                            lv_obj_set_size(obj, LV_SIZE_CONTENT, LV_SIZE_CONTENT);
                            lv_obj_set_style_text_font(obj, &lv_font_montserrat_44, LV_PART_MAIN | LV_STATE_DEFAULT);
                            lv_label_set_text(obj, "");
                        }
                        {
                            lv_obj_t *obj = lv_label_create(parent_obj);
                            lv_obj_set_pos(obj, 0, 0);
                            lv_obj_set_size(obj, LV_SIZE_CONTENT, LV_SIZE_CONTENT);
                            lv_obj_set_style_text_font(obj, &lv_font_montserrat_22, LV_PART_MAIN | LV_STATE_DEFAULT);
                            lv_label_set_text(obj, _("About"));
                        }
                        {
                            lv_obj_t *obj = lv_label_create(parent_obj);
                            lv_obj_set_pos(obj, 0, 0);
                            lv_obj_set_size(obj, LV_SIZE_CONTENT, LV_SIZE_CONTENT);
                            lv_label_set_text_static(obj, "Learn more about Helgatchi!");
                        }
                    }
                }
                {
                    // Admin Panel
                    lv_obj_t *obj = lv_obj_create(parent_obj);
                    objects.admin_panel = obj;
                    lv_obj_set_pos(obj, 14, 28);
                    lv_obj_set_size(obj, LV_PCT(100), LV_PCT(100));
                    lv_obj_add_event_cb(obj, event_handler_cb_main_menu_admin_panel, LV_EVENT_ALL, flowState);
                    lv_obj_add_flag(obj, LV_OBJ_FLAG_SCROLL_ON_FOCUS|LV_OBJ_FLAG_HIDDEN);
                    lv_obj_add_state(obj, LV_STATE_FOCUS_KEY);
                    add_style_default_main_menu_panel(obj);
                    {
                        lv_obj_t *parent_obj = obj;
                        {
                            lv_obj_t *obj = lv_label_create(parent_obj);
                            objects.obj15 = obj;
                            lv_obj_set_pos(obj, 0, 0);
                            lv_obj_set_size(obj, LV_SIZE_CONTENT, LV_SIZE_CONTENT);
                            lv_obj_set_style_text_font(obj, &lv_font_montserrat_44, LV_PART_MAIN | LV_STATE_DEFAULT);
                            lv_obj_set_style_text_color(obj, lv_color_hex(0xfafafa), LV_PART_MAIN | LV_STATE_DEFAULT);
                            lv_label_set_text(obj, "");
                        }
                        {
                            lv_obj_t *obj = lv_label_create(parent_obj);
                            lv_obj_set_pos(obj, 0, 0);
                            lv_obj_set_size(obj, LV_SIZE_CONTENT, LV_SIZE_CONTENT);
                            lv_obj_set_style_text_font(obj, &lv_font_montserrat_22, LV_PART_MAIN | LV_STATE_DEFAULT);
                            lv_label_set_text(obj, _("Admin"));
                        }
                        {
                            lv_obj_t *obj = lv_label_create(parent_obj);
                            lv_obj_set_pos(obj, 0, 0);
                            lv_obj_set_size(obj, LV_SIZE_CONTENT, LV_SIZE_CONTENT);
                            lv_label_set_text_static(obj, "Helga will tell others what to do!");
                        }
                    }
                }
                {
                    // Power Panel
                    lv_obj_t *obj = lv_obj_create(parent_obj);
                    objects.power_panel = obj;
                    lv_obj_set_pos(obj, 14, 28);
                    lv_obj_set_size(obj, LV_PCT(100), LV_PCT(100));
                    lv_obj_add_event_cb(obj, event_handler_cb_main_menu_power_panel, LV_EVENT_ALL, flowState);
                    lv_obj_add_flag(obj, LV_OBJ_FLAG_SCROLL_ON_FOCUS);
                    add_style_default_main_menu_panel(obj);
                    {
                        lv_obj_t *parent_obj = obj;
                        {
                            lv_obj_t *obj = lv_label_create(parent_obj);
                            objects.obj20 = obj;
                            lv_obj_set_pos(obj, 0, 0);
                            lv_obj_set_size(obj, LV_SIZE_CONTENT, LV_SIZE_CONTENT);
                            lv_obj_set_style_text_font(obj, &lv_font_montserrat_44, LV_PART_MAIN | LV_STATE_DEFAULT);
                            lv_label_set_text(obj, "");
                        }
                        {
                            lv_obj_t *obj = lv_label_create(parent_obj);
                            lv_obj_set_pos(obj, 0, 0);
                            lv_obj_set_size(obj, LV_SIZE_CONTENT, LV_SIZE_CONTENT);
                            lv_obj_set_style_text_font(obj, &lv_font_montserrat_22, LV_PART_MAIN | LV_STATE_DEFAULT);
                            lv_label_set_text(obj, _("Power"));
                        }
                        {
                            lv_obj_t *obj = lv_label_create(parent_obj);
                            lv_obj_set_pos(obj, 0, 0);
                            lv_obj_set_size(obj, LV_PCT(85), LV_SIZE_CONTENT);
                            lv_obj_set_style_text_align(obj, LV_TEXT_ALIGN_CENTER, LV_PART_MAIN | LV_STATE_DEFAULT);
                            lv_label_set_text_static(obj, "Power off, reboot, or sleep your Helgatchi!");
                        }
                    }
                }
            }
        }
    }
    
    tick_screen_main_menu();
}

void tick_screen_main_menu() {
    void *flowState = getFlowState(0, 0);
    (void)flowState;
    tick_user_widget_top_bar(getFlowState(flowState, 0), 16);
    {
        const char *new_val = evalTextProperty(flowState, 4, 3, "Failed to evaluate Text in Label widget");
        const char *cur_val = lv_label_get_text(objects.obj13);
        if (strcmp(new_val, cur_val) != 0) {
            tick_value_change_obj = objects.obj13;
            lv_label_set_text(objects.obj13, new_val);
            tick_value_change_obj = NULL;
        }
    }
    {
        const char *new_val = evalTextProperty(flowState, 8, 3, "Failed to evaluate Text in Label widget");
        const char *cur_val = lv_label_get_text(objects.obj14);
        if (strcmp(new_val, cur_val) != 0) {
            tick_value_change_obj = objects.obj14;
            lv_label_set_text(objects.obj14, new_val);
            tick_value_change_obj = NULL;
        }
    }
    {
        const char *new_val = evalTextProperty(flowState, 12, 3, "Failed to evaluate Text in Label widget");
        const char *cur_val = lv_label_get_text(objects.obj16);
        if (strcmp(new_val, cur_val) != 0) {
            tick_value_change_obj = objects.obj16;
            lv_label_set_text(objects.obj16, new_val);
            tick_value_change_obj = NULL;
        }
    }
    {
        const char *new_val = evalTextProperty(flowState, 16, 3, "Failed to evaluate Text in Label widget");
        const char *cur_val = lv_label_get_text(objects.obj17);
        if (strcmp(new_val, cur_val) != 0) {
            tick_value_change_obj = objects.obj17;
            lv_label_set_text(objects.obj17, new_val);
            tick_value_change_obj = NULL;
        }
    }
    {
        const char *new_val = evalTextProperty(flowState, 20, 3, "Failed to evaluate Text in Label widget");
        const char *cur_val = lv_label_get_text(objects.obj18);
        if (strcmp(new_val, cur_val) != 0) {
            tick_value_change_obj = objects.obj18;
            lv_label_set_text(objects.obj18, new_val);
            tick_value_change_obj = NULL;
        }
    }
    {
        const char *new_val = evalTextProperty(flowState, 24, 3, "Failed to evaluate Text in Label widget");
        const char *cur_val = lv_label_get_text(objects.obj19);
        if (strcmp(new_val, cur_val) != 0) {
            tick_value_change_obj = objects.obj19;
            lv_label_set_text(objects.obj19, new_val);
            tick_value_change_obj = NULL;
        }
    }
    {
        const char *new_val = evalTextProperty(flowState, 28, 3, "Failed to evaluate Text in Label widget");
        const char *cur_val = lv_label_get_text(objects.obj15);
        if (strcmp(new_val, cur_val) != 0) {
            tick_value_change_obj = objects.obj15;
            lv_label_set_text(objects.obj15, new_val);
            tick_value_change_obj = NULL;
        }
    }
    {
        const char *new_val = evalTextProperty(flowState, 32, 3, "Failed to evaluate Text in Label widget");
        const char *cur_val = lv_label_get_text(objects.obj20);
        if (strcmp(new_val, cur_val) != 0) {
            tick_value_change_obj = objects.obj20;
            lv_label_set_text(objects.obj20, new_val);
            tick_value_change_obj = NULL;
        }
    }
}

void create_screen_tutorial_splash_screen() {
    void *flowState = getFlowState(0, 1);
    (void)flowState;
    lv_obj_t *obj = lv_obj_create(0);
    objects.tutorial_splash_screen = obj;
    lv_obj_set_pos(obj, 0, 0);
    lv_obj_set_size(obj, 280, 240);
    lv_obj_add_event_cb(obj, event_handler_cb_tutorial_splash_screen_tutorial_splash_screen, LV_EVENT_ALL, flowState);
    {
        lv_obj_t *parent_obj = obj;
        {
            // Splash Screen Tutorial
            lv_obj_t *obj = lv_obj_create(parent_obj);
            objects.splash_screen_tutorial = obj;
            lv_obj_set_pos(obj, 0, 0);
            lv_obj_set_size(obj, LV_PCT(100), LV_PCT(100));
            lv_obj_set_style_pad_left(obj, 0, LV_PART_MAIN | LV_STATE_DEFAULT);
            lv_obj_set_style_pad_top(obj, 0, LV_PART_MAIN | LV_STATE_DEFAULT);
            lv_obj_set_style_pad_right(obj, 0, LV_PART_MAIN | LV_STATE_DEFAULT);
            lv_obj_set_style_pad_bottom(obj, 0, LV_PART_MAIN | LV_STATE_DEFAULT);
            lv_obj_set_style_bg_opa(obj, 0, LV_PART_MAIN | LV_STATE_DEFAULT);
            lv_obj_set_style_border_width(obj, 0, LV_PART_MAIN | LV_STATE_DEFAULT);
            lv_obj_set_style_radius(obj, 0, LV_PART_MAIN | LV_STATE_DEFAULT);
            {
                lv_obj_t *parent_obj = obj;
                {
                    lv_obj_t *obj = lv_image_create(parent_obj);
                    objects.obj21 = obj;
                    lv_obj_set_pos(obj, 0, -41);
                    lv_obj_set_size(obj, LV_SIZE_CONTENT, LV_SIZE_CONTENT);
                    lv_image_set_src(obj, &img_dc801_logo);
                    lv_image_set_inner_align(obj, LV_IMAGE_ALIGN_DEFAULT);
                    lv_obj_set_style_align(obj, LV_ALIGN_CENTER, LV_PART_MAIN | LV_STATE_DEFAULT);
                    lv_obj_set_style_image_recolor(obj, lv_color_hex(0xffffff), LV_PART_MAIN | LV_STATE_DEFAULT);
                }
                {
                    lv_obj_t *obj = lv_label_create(parent_obj);
                    lv_obj_set_pos(obj, 0, 4);
                    lv_obj_set_size(obj, LV_SIZE_CONTENT, LV_SIZE_CONTENT);
                    lv_obj_set_style_align(obj, LV_ALIGN_CENTER, LV_PART_MAIN | LV_STATE_DEFAULT);
                    lv_obj_set_style_text_font(obj, &lv_font_montserrat_22, LV_PART_MAIN | LV_STATE_DEFAULT);
                    lv_label_set_text_static(obj, "HELGATCHI V2");
                }
                {
                    // Start Tutorial Button
                    lv_obj_t *obj = lv_button_create(parent_obj);
                    objects.start_tutorial_button = obj;
                    lv_obj_set_pos(obj, 0, 45);
                    lv_obj_set_size(obj, LV_SIZE_CONTENT, LV_SIZE_CONTENT);
                    lv_obj_add_event_cb(obj, event_handler_cb_tutorial_splash_screen_start_tutorial_button, LV_EVENT_ALL, flowState);
                    lv_obj_add_state(obj, LV_STATE_FOCUS_KEY);
                    add_style_focused___button(obj);
                    lv_obj_set_style_align(obj, LV_ALIGN_CENTER, LV_PART_MAIN | LV_STATE_DEFAULT);
                    {
                        lv_obj_t *parent_obj = obj;
                        {
                            lv_obj_t *obj = lv_label_create(parent_obj);
                            objects.obj23 = obj;
                            lv_obj_set_pos(obj, 0, 0);
                            lv_obj_set_size(obj, LV_SIZE_CONTENT, LV_SIZE_CONTENT);
                            lv_obj_set_style_align(obj, LV_ALIGN_CENTER, LV_PART_MAIN | LV_STATE_DEFAULT);
                            lv_label_set_text(obj, "");
                        }
                    }
                }
                {
                    lv_obj_t *obj = lv_label_create(parent_obj);
                    objects.obj22 = obj;
                    lv_obj_set_pos(obj, 0, 80);
                    lv_obj_set_size(obj, LV_SIZE_CONTENT, LV_SIZE_CONTENT);
                    lv_obj_set_style_align(obj, LV_ALIGN_CENTER, LV_PART_MAIN | LV_STATE_DEFAULT);
                    lv_obj_set_style_text_color(obj, lv_color_hex(theme_colors[eez_flow_get_selected_theme_index()][2]), LV_PART_MAIN | LV_STATE_DEFAULT);
                    lv_obj_set_style_text_font(obj, &lv_font_montserrat_12, LV_PART_MAIN | LV_STATE_DEFAULT);
                    lv_obj_set_style_text_decor(obj, LV_TEXT_DECOR_NONE, LV_PART_MAIN | LV_STATE_DEFAULT);
                    lv_label_set_text_static(obj, "Press (BAAA) to begin");
                }
            }
        }
    }
    
    tick_screen_tutorial_splash_screen();
}

void tick_screen_tutorial_splash_screen() {
    void *flowState = getFlowState(0, 1);
    (void)flowState;
    {
        const char *new_val = evalTextProperty(flowState, 5, 3, "Failed to evaluate Text in Label widget");
        const char *cur_val = lv_label_get_text(objects.obj23);
        if (strcmp(new_val, cur_val) != 0) {
            tick_value_change_obj = objects.obj23;
            lv_label_set_text(objects.obj23, new_val);
            tick_value_change_obj = NULL;
        }
    }
}

void create_screen_tutorial() {
    void *flowState = getFlowState(0, 2);
    (void)flowState;
    lv_obj_t *obj = lv_obj_create(0);
    objects.tutorial = obj;
    lv_obj_set_pos(obj, 0, 0);
    lv_obj_set_size(obj, 280, 240);
    lv_obj_add_event_cb(obj, event_handler_cb_tutorial_tutorial, LV_EVENT_ALL, flowState);
    lv_obj_add_flag(obj, LV_OBJ_FLAG_SCROLL_ONE|LV_OBJ_FLAG_SCROLL_ON_FOCUS);
    {
        lv_obj_t *parent_obj = obj;
        {
            lv_obj_t *obj = lv_obj_create(parent_obj);
            lv_obj_set_pos(obj, 0, 0);
            lv_obj_set_size(obj, LV_PCT(100), LV_PCT(100));
            lv_obj_set_style_pad_left(obj, 0, LV_PART_MAIN | LV_STATE_DEFAULT);
            lv_obj_set_style_pad_top(obj, 0, LV_PART_MAIN | LV_STATE_DEFAULT);
            lv_obj_set_style_pad_right(obj, 0, LV_PART_MAIN | LV_STATE_DEFAULT);
            lv_obj_set_style_pad_bottom(obj, 0, LV_PART_MAIN | LV_STATE_DEFAULT);
            lv_obj_set_style_bg_opa(obj, 0, LV_PART_MAIN | LV_STATE_DEFAULT);
            lv_obj_set_style_border_width(obj, 0, LV_PART_MAIN | LV_STATE_DEFAULT);
            lv_obj_set_style_radius(obj, 0, LV_PART_MAIN | LV_STATE_DEFAULT);
            lv_obj_add_flag(obj, LV_OBJ_FLAG_SCROLL_ONE);
            lv_obj_remove_flag(obj, LV_OBJ_FLAG_SCROLL_CHAIN_VER);
            lv_obj_set_scrollbar_mode(obj, LV_SCROLLBAR_MODE_ON);
            lv_obj_set_scroll_dir(obj, LV_DIR_HOR);
            lv_obj_set_scroll_snap_x(obj, LV_SCROLL_SNAP_CENTER);
            lv_obj_set_style_layout(obj, LV_LAYOUT_FLEX, LV_PART_MAIN | LV_STATE_DEFAULT);
            lv_obj_set_style_flex_flow(obj, LV_FLEX_FLOW_ROW, LV_PART_MAIN | LV_STATE_DEFAULT);
            {
                lv_obj_t *parent_obj = obj;
                {
                    lv_obj_t *obj = lv_obj_create(parent_obj);
                    objects.obj43 = obj;
                    lv_obj_set_pos(obj, 0, 0);
                    lv_obj_set_size(obj, LV_PCT(100), LV_PCT(100));
                    lv_obj_add_flag(obj, LV_OBJ_FLAG_SCROLL_ON_FOCUS);
                    lv_obj_add_state(obj, LV_STATE_FOCUS_KEY);
                    add_style_default_main_menu_panel(obj);
                    {
                        lv_obj_t *parent_obj = obj;
                        {
                            lv_obj_t *obj = lv_label_create(parent_obj);
                            lv_obj_set_pos(obj, 0, 0);
                            lv_obj_set_size(obj, LV_SIZE_CONTENT, LV_SIZE_CONTENT);
                            lv_obj_set_style_text_font(obj, &lv_font_montserrat_24, LV_PART_MAIN | LV_STATE_DEFAULT);
                            lv_obj_set_style_text_decor(obj, LV_TEXT_DECOR_UNDERLINE, LV_PART_MAIN | LV_STATE_DEFAULT);
                            lv_label_set_text_static(obj, "Welcome!");
                        }
                        {
                            lv_obj_t *obj = lv_label_create(parent_obj);
                            objects.obj25 = obj;
                            lv_obj_set_pos(obj, 0, 0);
                            lv_obj_set_size(obj, LV_PCT(100), LV_SIZE_CONTENT);
                            lv_obj_set_style_text_align(obj, LV_TEXT_ALIGN_CENTER, LV_PART_MAIN | LV_STATE_DEFAULT);
                            lv_label_set_text(obj, "");
                        }
                    }
                }
                {
                    lv_obj_t *obj = lv_obj_create(parent_obj);
                    objects.obj44 = obj;
                    lv_obj_set_pos(obj, 0, 0);
                    lv_obj_set_size(obj, LV_PCT(100), LV_PCT(100));
                    lv_obj_add_flag(obj, LV_OBJ_FLAG_SCROLL_ON_FOCUS);
                    add_style_default_main_menu_panel(obj);
                    {
                        lv_obj_t *parent_obj = obj;
                        {
                            lv_obj_t *obj = lv_label_create(parent_obj);
                            lv_obj_set_pos(obj, 0, 0);
                            lv_obj_set_size(obj, LV_SIZE_CONTENT, LV_SIZE_CONTENT);
                            lv_obj_set_style_text_font(obj, &lv_font_montserrat_24, LV_PART_MAIN | LV_STATE_DEFAULT);
                            lv_obj_set_style_text_decor(obj, LV_TEXT_DECOR_UNDERLINE, LV_PART_MAIN | LV_STATE_DEFAULT);
                            lv_label_set_text_static(obj, "Buttons!");
                        }
                        {
                            lv_obj_t *obj = lv_label_create(parent_obj);
                            objects.obj26 = obj;
                            lv_obj_set_pos(obj, 0, 0);
                            lv_obj_set_size(obj, LV_PCT(100), LV_SIZE_CONTENT);
                            lv_obj_set_style_text_align(obj, LV_TEXT_ALIGN_CENTER, LV_PART_MAIN | LV_STATE_DEFAULT);
                            lv_label_set_text(obj, "");
                        }
                    }
                }
                {
                    lv_obj_t *obj = lv_obj_create(parent_obj);
                    objects.obj45 = obj;
                    lv_obj_set_pos(obj, 0, 0);
                    lv_obj_set_size(obj, LV_PCT(100), LV_PCT(100));
                    lv_obj_add_flag(obj, LV_OBJ_FLAG_SCROLL_ON_FOCUS);
                    add_style_default_main_menu_panel(obj);
                    {
                        lv_obj_t *parent_obj = obj;
                        {
                            lv_obj_t *obj = lv_label_create(parent_obj);
                            lv_obj_set_pos(obj, 0, 0);
                            lv_obj_set_size(obj, LV_SIZE_CONTENT, LV_SIZE_CONTENT);
                            lv_obj_set_style_text_font(obj, &lv_font_montserrat_24, LV_PART_MAIN | LV_STATE_DEFAULT);
                            lv_obj_set_style_text_decor(obj, LV_TEXT_DECOR_UNDERLINE, LV_PART_MAIN | LV_STATE_DEFAULT);
                            lv_label_set_text_static(obj, "About your device");
                        }
                        {
                            lv_obj_t *obj = lv_label_create(parent_obj);
                            lv_obj_set_pos(obj, 0, 0);
                            lv_obj_set_size(obj, LV_PCT(100), LV_SIZE_CONTENT);
                            lv_obj_set_style_text_align(obj, LV_TEXT_ALIGN_CENTER, LV_PART_MAIN | LV_STATE_DEFAULT);
                            lv_label_set_text_static(obj, "The Helgatchi is powered by the Seeed XIAO ESP32-S3. \n\nIt features an external RP-SMA connector, so you can connect any 2.4Ghz antenna you desire!");
                        }
                    }
                }
                {
                    lv_obj_t *obj = lv_obj_create(parent_obj);
                    objects.obj46 = obj;
                    lv_obj_set_pos(obj, 0, 0);
                    lv_obj_set_size(obj, LV_PCT(100), LV_PCT(100));
                    lv_obj_add_flag(obj, LV_OBJ_FLAG_SCROLL_ON_FOCUS);
                    add_style_default_main_menu_panel(obj);
                    {
                        lv_obj_t *parent_obj = obj;
                        {
                            lv_obj_t *obj = lv_label_create(parent_obj);
                            lv_obj_set_pos(obj, 0, 0);
                            lv_obj_set_size(obj, LV_SIZE_CONTENT, LV_SIZE_CONTENT);
                            lv_obj_set_style_text_font(obj, &lv_font_montserrat_24, LV_PART_MAIN | LV_STATE_DEFAULT);
                            lv_obj_set_style_text_decor(obj, LV_TEXT_DECOR_UNDERLINE, LV_PART_MAIN | LV_STATE_DEFAULT);
                            lv_label_set_text_static(obj, "Behavior");
                        }
                        {
                            lv_obj_t *obj = lv_label_create(parent_obj);
                            lv_obj_set_pos(obj, 0, 0);
                            lv_obj_set_size(obj, LV_PCT(100), LV_SIZE_CONTENT);
                            lv_obj_set_style_text_align(obj, LV_TEXT_ALIGN_CENTER, LV_PART_MAIN | LV_STATE_DEFAULT);
                            lv_label_set_text_static(obj, "Your Helgatchi will automatically scan for all nearby BT and WiFi signals. You can change this behavior in the device settings, disabling BT or WiFi Scanning.\n\nYour Helgatchi will sleep automatically. To wake it up, press and hold the Center button until the screen wakes.");
                        }
                    }
                }
                {
                    lv_obj_t *obj = lv_obj_create(parent_obj);
                    objects.obj47 = obj;
                    lv_obj_set_pos(obj, 0, 0);
                    lv_obj_set_size(obj, LV_PCT(100), LV_PCT(100));
                    lv_obj_add_flag(obj, LV_OBJ_FLAG_SCROLL_ON_FOCUS);
                    add_style_default_main_menu_panel(obj);
                    {
                        lv_obj_t *parent_obj = obj;
                        {
                            lv_obj_t *obj = lv_label_create(parent_obj);
                            lv_obj_set_pos(obj, 0, 0);
                            lv_obj_set_size(obj, LV_SIZE_CONTENT, LV_SIZE_CONTENT);
                            lv_obj_set_style_text_font(obj, &lv_font_montserrat_24, LV_PART_MAIN | LV_STATE_DEFAULT);
                            lv_obj_set_style_text_decor(obj, LV_TEXT_DECOR_UNDERLINE, LV_PART_MAIN | LV_STATE_DEFAULT);
                            lv_label_set_text_static(obj, "More information");
                        }
                        {
                            lv_obj_t *obj = lv_label_create(parent_obj);
                            lv_obj_set_pos(obj, 0, 0);
                            lv_obj_set_size(obj, LV_SIZE_CONTENT, LV_SIZE_CONTENT);
                            lv_label_set_text_static(obj, "Scan to view the Github project");
                        }
                        {
                            lv_obj_t *obj = lv_qrcode_create(parent_obj);
                            objects.obj24 = obj;
                            lv_obj_set_pos(obj, 0, 0);
                            lv_obj_set_size(obj, 150, 150);
                            lv_qrcode_set_size(obj, 150);
                            lv_qrcode_set_dark_color(obj, lv_color_hex(0x000000));
                            lv_qrcode_set_light_color(obj, lv_color_hex(0xffffff));
                            lv_qrcode_update(obj, "https://github.com/pips801/Helgatchi", 36);
                            lv_obj_add_flag(obj, LV_OBJ_FLAG_CLICKABLE);
                        }
                    }
                }
                {
                    lv_obj_t *obj = lv_obj_create(parent_obj);
                    lv_obj_set_pos(obj, 0, 0);
                    lv_obj_set_size(obj, LV_PCT(100), LV_PCT(100));
                    lv_obj_add_flag(obj, LV_OBJ_FLAG_SCROLL_ON_FOCUS);
                    add_style_default_main_menu_panel(obj);
                    {
                        lv_obj_t *parent_obj = obj;
                        {
                            lv_obj_t *obj = lv_label_create(parent_obj);
                            lv_obj_set_pos(obj, 0, 0);
                            lv_obj_set_size(obj, LV_SIZE_CONTENT, LV_SIZE_CONTENT);
                            lv_obj_set_style_text_font(obj, &lv_font_montserrat_24, LV_PART_MAIN | LV_STATE_DEFAULT);
                            lv_obj_set_style_text_decor(obj, LV_TEXT_DECOR_UNDERLINE, LV_PART_MAIN | LV_STATE_DEFAULT);
                            lv_label_set_text_static(obj, "Lets start scanning!");
                        }
                        {
                            lv_obj_t *obj = lv_label_create(parent_obj);
                            lv_obj_set_pos(obj, 0, 0);
                            lv_obj_set_size(obj, LV_PCT(100), LV_SIZE_CONTENT);
                            lv_obj_set_style_text_align(obj, LV_TEXT_ALIGN_CENTER, LV_PART_MAIN | LV_STATE_DEFAULT);
                            lv_label_set_text_static(obj, "Thanks for learning about the Helgatchi! ");
                        }
                        {
                            // End tutorial button
                            lv_obj_t *obj = lv_button_create(parent_obj);
                            objects.end_tutorial_button = obj;
                            lv_obj_set_pos(obj, 0, 0);
                            lv_obj_set_size(obj, LV_SIZE_CONTENT, LV_SIZE_CONTENT);
                            lv_obj_add_event_cb(obj, event_handler_cb_tutorial_end_tutorial_button, LV_EVENT_ALL, flowState);
                            add_style_focused___button(obj);
                            {
                                lv_obj_t *parent_obj = obj;
                                {
                                    lv_obj_t *obj = lv_label_create(parent_obj);
                                    objects.obj27 = obj;
                                    lv_obj_set_pos(obj, 0, 0);
                                    lv_obj_set_size(obj, LV_SIZE_CONTENT, LV_SIZE_CONTENT);
                                    lv_obj_set_style_align(obj, LV_ALIGN_CENTER, LV_PART_MAIN | LV_STATE_DEFAULT);
                                    lv_label_set_text(obj, "");
                                }
                            }
                        }
                    }
                }
            }
        }
    }
    
    tick_screen_tutorial();
}

void tick_screen_tutorial() {
    void *flowState = getFlowState(0, 2);
    (void)flowState;
    {
        const char *new_val = evalTextProperty(flowState, 4, 3, "Failed to evaluate Text in Label widget");
        const char *cur_val = lv_label_get_text(objects.obj25);
        if (strcmp(new_val, cur_val) != 0) {
            tick_value_change_obj = objects.obj25;
            lv_label_set_text(objects.obj25, new_val);
            tick_value_change_obj = NULL;
        }
    }
    {
        const char *new_val = evalTextProperty(flowState, 7, 3, "Failed to evaluate Text in Label widget");
        const char *cur_val = lv_label_get_text(objects.obj26);
        if (strcmp(new_val, cur_val) != 0) {
            tick_value_change_obj = objects.obj26;
            lv_label_set_text(objects.obj26, new_val);
            tick_value_change_obj = NULL;
        }
    }
    {
        const char *new_val = evalTextProperty(flowState, 22, 3, "Failed to evaluate Text in Label widget");
        const char *cur_val = lv_label_get_text(objects.obj27);
        if (strcmp(new_val, cur_val) != 0) {
            tick_value_change_obj = objects.obj27;
            lv_label_set_text(objects.obj27, new_val);
            tick_value_change_obj = NULL;
        }
    }
}

void create_screen_settings() {
    void *flowState = getFlowState(0, 3);
    (void)flowState;
    lv_obj_t *obj = lv_obj_create(0);
    objects.settings = obj;
    lv_obj_set_pos(obj, 0, 0);
    lv_obj_set_size(obj, 280, 240);
    lv_obj_add_event_cb(obj, event_handler_cb_settings_settings, LV_EVENT_ALL, flowState);
    lv_obj_remove_flag(obj, LV_OBJ_FLAG_SCROLLABLE);
    {
        lv_obj_t *parent_obj = obj;
        {
            // Settings Top Bar
            lv_obj_t *obj = lv_obj_create(parent_obj);
            objects.settings_top_bar = obj;
            lv_obj_set_pos(obj, 0, 0);
            lv_obj_set_size(obj, 280, 36);
            lv_obj_set_style_pad_left(obj, 0, LV_PART_MAIN | LV_STATE_DEFAULT);
            lv_obj_set_style_pad_top(obj, 0, LV_PART_MAIN | LV_STATE_DEFAULT);
            lv_obj_set_style_pad_right(obj, 0, LV_PART_MAIN | LV_STATE_DEFAULT);
            lv_obj_set_style_pad_bottom(obj, 0, LV_PART_MAIN | LV_STATE_DEFAULT);
            lv_obj_set_style_bg_opa(obj, 0, LV_PART_MAIN | LV_STATE_DEFAULT);
            lv_obj_set_style_border_width(obj, 0, LV_PART_MAIN | LV_STATE_DEFAULT);
            create_user_widget_top_bar(obj, getFlowState(flowState, 0), 21);
            lv_obj_add_flag(obj, LV_OBJ_FLAG_FLOATING);
        }
        {
            lv_obj_t *obj = lv_obj_create(parent_obj);
            lv_obj_set_pos(obj, 0, 0);
            lv_obj_set_size(obj, LV_PCT(100), LV_PCT(85));
            lv_obj_remove_flag(obj, LV_OBJ_FLAG_SCROLL_CHAIN_VER);
            lv_obj_set_scrollbar_mode(obj, LV_SCROLLBAR_MODE_AUTO);
            lv_obj_set_scroll_dir(obj, LV_DIR_VER);
            lv_obj_set_scroll_snap_x(obj, LV_SCROLL_SNAP_NONE);
            lv_obj_set_scroll_snap_y(obj, LV_SCROLL_SNAP_CENTER);
            lv_obj_set_style_radius(obj, 20, LV_PART_MAIN | LV_STATE_DEFAULT);
            lv_obj_set_style_layout(obj, LV_LAYOUT_FLEX, LV_PART_MAIN | LV_STATE_DEFAULT);
            lv_obj_set_style_flex_flow(obj, LV_FLEX_FLOW_COLUMN, LV_PART_MAIN | LV_STATE_DEFAULT);
            lv_obj_set_style_flex_cross_place(obj, LV_FLEX_ALIGN_CENTER, LV_PART_MAIN | LV_STATE_DEFAULT);
            lv_obj_set_style_pad_top(obj, 5, LV_PART_MAIN | LV_STATE_DEFAULT);
            lv_obj_set_style_pad_bottom(obj, 5, LV_PART_MAIN | LV_STATE_DEFAULT);
            lv_obj_set_style_pad_left(obj, 12, LV_PART_MAIN | LV_STATE_DEFAULT);
            lv_obj_set_style_align(obj, LV_ALIGN_BOTTOM_MID, LV_PART_MAIN | LV_STATE_DEFAULT);
            lv_obj_set_style_pad_right(obj, 12, LV_PART_MAIN | LV_STATE_DEFAULT);
            lv_obj_set_style_pad_top(obj, 4, LV_PART_SCROLLBAR | LV_STATE_DEFAULT);
            lv_obj_set_style_pad_bottom(obj, 4, LV_PART_SCROLLBAR | LV_STATE_DEFAULT);
            lv_obj_set_style_pad_left(obj, 6, LV_PART_SCROLLBAR | LV_STATE_DEFAULT);
            lv_obj_set_style_pad_right(obj, 6, LV_PART_SCROLLBAR | LV_STATE_DEFAULT);
            {
                lv_obj_t *parent_obj = obj;
                {
                    lv_obj_t *obj = lv_label_create(parent_obj);
                    lv_obj_set_pos(obj, 0, 0);
                    lv_obj_set_size(obj, LV_SIZE_CONTENT, LV_SIZE_CONTENT);
                    lv_obj_set_style_text_decor(obj, LV_TEXT_DECOR_UNDERLINE, LV_PART_MAIN | LV_STATE_DEFAULT);
                    lv_label_set_text_static(obj, "Screen & LEDs");
                }
                {
                    lv_obj_t *obj = lv_obj_create(parent_obj);
                    lv_obj_set_pos(obj, 0, 0);
                    lv_obj_set_size(obj, LV_PCT(100), LV_SIZE_CONTENT);
                    lv_obj_set_style_pad_left(obj, 0, LV_PART_MAIN | LV_STATE_DEFAULT);
                    lv_obj_set_style_pad_top(obj, 0, LV_PART_MAIN | LV_STATE_DEFAULT);
                    lv_obj_set_style_pad_right(obj, 0, LV_PART_MAIN | LV_STATE_DEFAULT);
                    lv_obj_set_style_pad_bottom(obj, 0, LV_PART_MAIN | LV_STATE_DEFAULT);
                    lv_obj_set_style_bg_opa(obj, 0, LV_PART_MAIN | LV_STATE_DEFAULT);
                    lv_obj_set_style_border_width(obj, 0, LV_PART_MAIN | LV_STATE_DEFAULT);
                    lv_obj_set_style_radius(obj, 0, LV_PART_MAIN | LV_STATE_DEFAULT);
                    lv_obj_add_flag(obj, LV_OBJ_FLAG_OVERFLOW_VISIBLE);
                    {
                        lv_obj_t *parent_obj = obj;
                        {
                            lv_obj_t *obj = lv_label_create(parent_obj);
                            lv_obj_set_pos(obj, 0, 0);
                            lv_obj_set_size(obj, LV_SIZE_CONTENT, LV_SIZE_CONTENT);
                            lv_obj_set_style_align(obj, LV_ALIGN_LEFT_MID, LV_PART_MAIN | LV_STATE_DEFAULT);
                            lv_label_set_text_static(obj, "Screen Brightness");
                        }
                        {
                            // Screen Brightness Dropdown
                            lv_obj_t *obj = lv_dropdown_create(parent_obj);
                            objects.screen_brightness_dropdown = obj;
                            lv_obj_set_pos(obj, 0, 0);
                            lv_obj_set_size(obj, LV_PCT(45), LV_SIZE_CONTENT);
                            lv_dropdown_set_options_static(obj, "Low\nMedium\nHigh\nMax");
                            lv_dropdown_set_selected(obj, 0);
                            lv_obj_add_flag(obj, LV_OBJ_FLAG_OVERFLOW_VISIBLE);
                            lv_obj_add_state(obj, LV_STATE_FOCUS_KEY);
                            add_style_focused___dropdown(obj);
                        }
                    }
                }
                {
                    lv_obj_t *obj = lv_obj_create(parent_obj);
                    lv_obj_set_pos(obj, 0, 0);
                    lv_obj_set_size(obj, LV_PCT(100), LV_SIZE_CONTENT);
                    lv_obj_set_style_pad_left(obj, 0, LV_PART_MAIN | LV_STATE_DEFAULT);
                    lv_obj_set_style_pad_top(obj, 0, LV_PART_MAIN | LV_STATE_DEFAULT);
                    lv_obj_set_style_pad_right(obj, 0, LV_PART_MAIN | LV_STATE_DEFAULT);
                    lv_obj_set_style_pad_bottom(obj, 0, LV_PART_MAIN | LV_STATE_DEFAULT);
                    lv_obj_set_style_bg_opa(obj, 0, LV_PART_MAIN | LV_STATE_DEFAULT);
                    lv_obj_set_style_border_width(obj, 0, LV_PART_MAIN | LV_STATE_DEFAULT);
                    lv_obj_set_style_radius(obj, 0, LV_PART_MAIN | LV_STATE_DEFAULT);
                    lv_obj_add_flag(obj, LV_OBJ_FLAG_OVERFLOW_VISIBLE);
                    {
                        lv_obj_t *parent_obj = obj;
                        {
                            lv_obj_t *obj = lv_label_create(parent_obj);
                            lv_obj_set_pos(obj, 0, 0);
                            lv_obj_set_size(obj, LV_SIZE_CONTENT, LV_SIZE_CONTENT);
                            lv_obj_set_style_align(obj, LV_ALIGN_LEFT_MID, LV_PART_MAIN | LV_STATE_DEFAULT);
                            lv_label_set_text_static(obj, "LED Brightness");
                        }
                        {
                            // LED Brightness Dropdown
                            lv_obj_t *obj = lv_dropdown_create(parent_obj);
                            objects.led_brightness_dropdown = obj;
                            lv_obj_set_pos(obj, 0, 0);
                            lv_obj_set_size(obj, LV_PCT(45), LV_SIZE_CONTENT);
                            lv_dropdown_set_options_static(obj, "Low\nMedium\nHigh\nMax");
                            lv_dropdown_set_selected(obj, 0);
                            lv_obj_add_flag(obj, LV_OBJ_FLAG_OVERFLOW_VISIBLE);
                            add_style_focused___dropdown(obj);
                        }
                    }
                }
                {
                    lv_obj_t *obj = lv_label_create(parent_obj);
                    lv_obj_set_pos(obj, 0, 0);
                    lv_obj_set_size(obj, LV_SIZE_CONTENT, LV_SIZE_CONTENT);
                    lv_obj_set_style_text_decor(obj, LV_TEXT_DECOR_UNDERLINE, LV_PART_MAIN | LV_STATE_DEFAULT);
                    lv_label_set_text_static(obj, "Alert Behavior");
                }
                {
                    lv_obj_t *obj = lv_obj_create(parent_obj);
                    lv_obj_set_pos(obj, 0, 0);
                    lv_obj_set_size(obj, LV_PCT(100), LV_SIZE_CONTENT);
                    lv_obj_set_style_pad_left(obj, 0, LV_PART_MAIN | LV_STATE_DEFAULT);
                    lv_obj_set_style_pad_top(obj, 0, LV_PART_MAIN | LV_STATE_DEFAULT);
                    lv_obj_set_style_pad_right(obj, 0, LV_PART_MAIN | LV_STATE_DEFAULT);
                    lv_obj_set_style_pad_bottom(obj, 0, LV_PART_MAIN | LV_STATE_DEFAULT);
                    lv_obj_set_style_bg_opa(obj, 0, LV_PART_MAIN | LV_STATE_DEFAULT);
                    lv_obj_set_style_border_width(obj, 0, LV_PART_MAIN | LV_STATE_DEFAULT);
                    lv_obj_set_style_radius(obj, 0, LV_PART_MAIN | LV_STATE_DEFAULT);
                    {
                        lv_obj_t *parent_obj = obj;
                        {
                            lv_obj_t *obj = lv_label_create(parent_obj);
                            lv_obj_set_pos(obj, 0, 0);
                            lv_obj_set_size(obj, LV_SIZE_CONTENT, LV_SIZE_CONTENT);
                            lv_obj_set_style_align(obj, LV_ALIGN_LEFT_MID, LV_PART_MAIN | LV_STATE_DEFAULT);
                            lv_label_set_text_static(obj, "Vibrate on Alert");
                        }
                        {
                            // Vibrate on Alert Switch
                            lv_obj_t *obj = lv_switch_create(parent_obj);
                            objects.vibrate_on_alert_switch = obj;
                            lv_obj_set_pos(obj, 0, 0);
                            lv_obj_set_size(obj, 50, 25);
                            add_style_focused___switch(obj);
                            lv_obj_set_style_align(obj, LV_ALIGN_RIGHT_MID, LV_PART_MAIN | LV_STATE_DEFAULT);
                        }
                    }
                }
                {
                    lv_obj_t *obj = lv_obj_create(parent_obj);
                    lv_obj_set_pos(obj, 0, 0);
                    lv_obj_set_size(obj, LV_PCT(100), LV_SIZE_CONTENT);
                    lv_obj_set_style_pad_left(obj, 0, LV_PART_MAIN | LV_STATE_DEFAULT);
                    lv_obj_set_style_pad_top(obj, 0, LV_PART_MAIN | LV_STATE_DEFAULT);
                    lv_obj_set_style_pad_right(obj, 0, LV_PART_MAIN | LV_STATE_DEFAULT);
                    lv_obj_set_style_pad_bottom(obj, 0, LV_PART_MAIN | LV_STATE_DEFAULT);
                    lv_obj_set_style_bg_opa(obj, 0, LV_PART_MAIN | LV_STATE_DEFAULT);
                    lv_obj_set_style_border_width(obj, 0, LV_PART_MAIN | LV_STATE_DEFAULT);
                    lv_obj_set_style_radius(obj, 0, LV_PART_MAIN | LV_STATE_DEFAULT);
                    {
                        lv_obj_t *parent_obj = obj;
                        {
                            lv_obj_t *obj = lv_label_create(parent_obj);
                            lv_obj_set_pos(obj, 0, 0);
                            lv_obj_set_size(obj, LV_SIZE_CONTENT, LV_SIZE_CONTENT);
                            lv_obj_set_style_align(obj, LV_ALIGN_LEFT_MID, LV_PART_MAIN | LV_STATE_DEFAULT);
                            lv_label_set_text_static(obj, "LEDs on Alert");
                        }
                        {
                            // LEDs on Alert Switch
                            lv_obj_t *obj = lv_switch_create(parent_obj);
                            objects.le_ds_on_alert_switch = obj;
                            lv_obj_set_pos(obj, 0, 0);
                            lv_obj_set_size(obj, 50, 25);
                            add_style_focused___switch(obj);
                            lv_obj_set_style_align(obj, LV_ALIGN_RIGHT_MID, LV_PART_MAIN | LV_STATE_DEFAULT);
                        }
                    }
                }
                {
                    lv_obj_t *obj = lv_obj_create(parent_obj);
                    lv_obj_set_pos(obj, 0, 0);
                    lv_obj_set_size(obj, LV_PCT(100), LV_SIZE_CONTENT);
                    lv_obj_set_style_pad_left(obj, 0, LV_PART_MAIN | LV_STATE_DEFAULT);
                    lv_obj_set_style_pad_top(obj, 0, LV_PART_MAIN | LV_STATE_DEFAULT);
                    lv_obj_set_style_pad_right(obj, 0, LV_PART_MAIN | LV_STATE_DEFAULT);
                    lv_obj_set_style_pad_bottom(obj, 0, LV_PART_MAIN | LV_STATE_DEFAULT);
                    lv_obj_set_style_bg_opa(obj, 0, LV_PART_MAIN | LV_STATE_DEFAULT);
                    lv_obj_set_style_border_width(obj, 0, LV_PART_MAIN | LV_STATE_DEFAULT);
                    lv_obj_set_style_radius(obj, 0, LV_PART_MAIN | LV_STATE_DEFAULT);
                    {
                        lv_obj_t *parent_obj = obj;
                        {
                            lv_obj_t *obj = lv_label_create(parent_obj);
                            lv_obj_set_pos(obj, 0, 0);
                            lv_obj_set_size(obj, LV_SIZE_CONTENT, LV_SIZE_CONTENT);
                            lv_obj_set_style_align(obj, LV_ALIGN_LEFT_MID, LV_PART_MAIN | LV_STATE_DEFAULT);
                            lv_label_set_text_static(obj, "Wake Screen on Alert");
                        }
                        {
                            // Wake Screen on Alert Switch
                            lv_obj_t *obj = lv_switch_create(parent_obj);
                            objects.wake_screen_on_alert_switch = obj;
                            lv_obj_set_pos(obj, 0, 0);
                            lv_obj_set_size(obj, 50, 25);
                            lv_obj_add_event_cb(obj, event_handler_cb_settings_wake_screen_on_alert_switch, LV_EVENT_ALL, flowState);
                            add_style_focused___switch(obj);
                            lv_obj_set_style_align(obj, LV_ALIGN_RIGHT_MID, LV_PART_MAIN | LV_STATE_DEFAULT);
                        }
                    }
                }
                {
                    lv_obj_t *obj = lv_obj_create(parent_obj);
                    lv_obj_set_pos(obj, 0, 0);
                    lv_obj_set_size(obj, LV_PCT(100), LV_SIZE_CONTENT);
                    lv_obj_set_style_pad_left(obj, 0, LV_PART_MAIN | LV_STATE_DEFAULT);
                    lv_obj_set_style_pad_top(obj, 0, LV_PART_MAIN | LV_STATE_DEFAULT);
                    lv_obj_set_style_pad_right(obj, 0, LV_PART_MAIN | LV_STATE_DEFAULT);
                    lv_obj_set_style_pad_bottom(obj, 0, LV_PART_MAIN | LV_STATE_DEFAULT);
                    lv_obj_set_style_bg_opa(obj, 0, LV_PART_MAIN | LV_STATE_DEFAULT);
                    lv_obj_set_style_border_width(obj, 0, LV_PART_MAIN | LV_STATE_DEFAULT);
                    lv_obj_set_style_radius(obj, 0, LV_PART_MAIN | LV_STATE_DEFAULT);
                    {
                        lv_obj_t *parent_obj = obj;
                        {
                            lv_obj_t *obj = lv_label_create(parent_obj);
                            objects.obj28 = obj;
                            lv_obj_set_pos(obj, 0, 0);
                            lv_obj_set_size(obj, LV_SIZE_CONTENT, LV_SIZE_CONTENT);
                            lv_obj_set_style_align(obj, LV_ALIGN_LEFT_MID, LV_PART_MAIN | LV_STATE_DEFAULT);
                            lv_obj_set_style_text_color(obj, lv_color_hex(theme_colors[eez_flow_get_selected_theme_index()][2]), LV_PART_MAIN | LV_STATE_DISABLED);
                            lv_label_set_text_static(obj, "Focus on Alerts page");
                        }
                        {
                            // Focus on alert page switch
                            lv_obj_t *obj = lv_switch_create(parent_obj);
                            objects.focus_on_alert_page_switch = obj;
                            lv_obj_set_pos(obj, 0, 0);
                            lv_obj_set_size(obj, 50, 25);
                            add_style_focused___switch(obj);
                        }
                    }
                }
                {
                    lv_obj_t *obj = lv_label_create(parent_obj);
                    lv_obj_set_pos(obj, 0, 0);
                    lv_obj_set_size(obj, LV_SIZE_CONTENT, LV_SIZE_CONTENT);
                    lv_obj_set_style_text_decor(obj, LV_TEXT_DECOR_UNDERLINE, LV_PART_MAIN | LV_STATE_DEFAULT);
                    lv_label_set_text_static(obj, "Scanning & Performance");
                }
                {
                    lv_obj_t *obj = lv_obj_create(parent_obj);
                    lv_obj_set_pos(obj, 0, 0);
                    lv_obj_set_size(obj, LV_PCT(100), LV_SIZE_CONTENT);
                    lv_obj_set_style_pad_left(obj, 0, LV_PART_MAIN | LV_STATE_DEFAULT);
                    lv_obj_set_style_pad_top(obj, 0, LV_PART_MAIN | LV_STATE_DEFAULT);
                    lv_obj_set_style_pad_right(obj, 0, LV_PART_MAIN | LV_STATE_DEFAULT);
                    lv_obj_set_style_pad_bottom(obj, 0, LV_PART_MAIN | LV_STATE_DEFAULT);
                    lv_obj_set_style_bg_opa(obj, 0, LV_PART_MAIN | LV_STATE_DEFAULT);
                    lv_obj_set_style_border_width(obj, 0, LV_PART_MAIN | LV_STATE_DEFAULT);
                    lv_obj_set_style_radius(obj, 0, LV_PART_MAIN | LV_STATE_DEFAULT);
                    {
                        lv_obj_t *parent_obj = obj;
                        {
                            lv_obj_t *obj = lv_label_create(parent_obj);
                            objects.obj29 = obj;
                            lv_obj_set_pos(obj, 0, 0);
                            lv_obj_set_size(obj, LV_SIZE_CONTENT, LV_SIZE_CONTENT);
                            lv_obj_set_style_align(obj, LV_ALIGN_LEFT_MID, LV_PART_MAIN | LV_STATE_DEFAULT);
                            lv_label_set_text(obj, "");
                        }
                        {
                            // BLE Scanning Switch
                            lv_obj_t *obj = lv_switch_create(parent_obj);
                            objects.ble_scanning_switch = obj;
                            lv_obj_set_pos(obj, 0, 0);
                            lv_obj_set_size(obj, 50, 25);
                            add_style_focused___switch(obj);
                        }
                    }
                }
                {
                    lv_obj_t *obj = lv_obj_create(parent_obj);
                    lv_obj_set_pos(obj, 0, 0);
                    lv_obj_set_size(obj, LV_PCT(100), LV_SIZE_CONTENT);
                    lv_obj_set_style_pad_left(obj, 0, LV_PART_MAIN | LV_STATE_DEFAULT);
                    lv_obj_set_style_pad_top(obj, 0, LV_PART_MAIN | LV_STATE_DEFAULT);
                    lv_obj_set_style_pad_right(obj, 0, LV_PART_MAIN | LV_STATE_DEFAULT);
                    lv_obj_set_style_pad_bottom(obj, 0, LV_PART_MAIN | LV_STATE_DEFAULT);
                    lv_obj_set_style_bg_opa(obj, 0, LV_PART_MAIN | LV_STATE_DEFAULT);
                    lv_obj_set_style_border_width(obj, 0, LV_PART_MAIN | LV_STATE_DEFAULT);
                    lv_obj_set_style_radius(obj, 0, LV_PART_MAIN | LV_STATE_DEFAULT);
                    {
                        lv_obj_t *parent_obj = obj;
                        {
                            lv_obj_t *obj = lv_label_create(parent_obj);
                            objects.obj30 = obj;
                            lv_obj_set_pos(obj, 0, 0);
                            lv_obj_set_size(obj, LV_SIZE_CONTENT, LV_SIZE_CONTENT);
                            lv_obj_set_style_align(obj, LV_ALIGN_LEFT_MID, LV_PART_MAIN | LV_STATE_DEFAULT);
                            lv_label_set_text(obj, "");
                        }
                        {
                            // Active BLE Scanning
                            lv_obj_t *obj = lv_switch_create(parent_obj);
                            objects.active_ble_scanning = obj;
                            lv_obj_set_pos(obj, 0, 0);
                            lv_obj_set_size(obj, 50, 25);
                            add_style_focused___switch(obj);
                        }
                    }
                }
                {
                    lv_obj_t *obj = lv_obj_create(parent_obj);
                    lv_obj_set_pos(obj, 0, 0);
                    lv_obj_set_size(obj, LV_PCT(100), LV_SIZE_CONTENT);
                    lv_obj_set_style_pad_left(obj, 0, LV_PART_MAIN | LV_STATE_DEFAULT);
                    lv_obj_set_style_pad_top(obj, 0, LV_PART_MAIN | LV_STATE_DEFAULT);
                    lv_obj_set_style_pad_right(obj, 0, LV_PART_MAIN | LV_STATE_DEFAULT);
                    lv_obj_set_style_pad_bottom(obj, 0, LV_PART_MAIN | LV_STATE_DEFAULT);
                    lv_obj_set_style_bg_opa(obj, 0, LV_PART_MAIN | LV_STATE_DEFAULT);
                    lv_obj_set_style_border_width(obj, 0, LV_PART_MAIN | LV_STATE_DEFAULT);
                    lv_obj_set_style_radius(obj, 0, LV_PART_MAIN | LV_STATE_DEFAULT);
                    {
                        lv_obj_t *parent_obj = obj;
                        {
                            lv_obj_t *obj = lv_label_create(parent_obj);
                            objects.obj31 = obj;
                            lv_obj_set_pos(obj, 0, 0);
                            lv_obj_set_size(obj, 180, LV_SIZE_CONTENT);
                            lv_obj_set_style_align(obj, LV_ALIGN_LEFT_MID, LV_PART_MAIN | LV_STATE_DEFAULT);
                            lv_label_set_text(obj, "");
                        }
                        {
                            // Ignore nameless random MACs
                            lv_obj_t *obj = lv_switch_create(parent_obj);
                            objects.ignore_nameless_random_ma_cs = obj;
                            lv_obj_set_pos(obj, 0, 0);
                            lv_obj_set_size(obj, 50, 25);
                            add_style_focused___switch(obj);
                        }
                    }
                }
                {
                    lv_obj_t *obj = lv_obj_create(parent_obj);
                    lv_obj_set_pos(obj, 0, 0);
                    lv_obj_set_size(obj, LV_PCT(100), LV_SIZE_CONTENT);
                    lv_obj_set_style_pad_left(obj, 0, LV_PART_MAIN | LV_STATE_DEFAULT);
                    lv_obj_set_style_pad_top(obj, 0, LV_PART_MAIN | LV_STATE_DEFAULT);
                    lv_obj_set_style_pad_right(obj, 0, LV_PART_MAIN | LV_STATE_DEFAULT);
                    lv_obj_set_style_pad_bottom(obj, 0, LV_PART_MAIN | LV_STATE_DEFAULT);
                    lv_obj_set_style_bg_opa(obj, 0, LV_PART_MAIN | LV_STATE_DEFAULT);
                    lv_obj_set_style_border_width(obj, 0, LV_PART_MAIN | LV_STATE_DEFAULT);
                    lv_obj_set_style_radius(obj, 0, LV_PART_MAIN | LV_STATE_DEFAULT);
                    {
                        lv_obj_t *parent_obj = obj;
                        {
                            lv_obj_t *obj = lv_label_create(parent_obj);
                            objects.obj32 = obj;
                            lv_obj_set_pos(obj, 0, 0);
                            lv_obj_set_size(obj, LV_SIZE_CONTENT, LV_SIZE_CONTENT);
                            lv_obj_set_style_align(obj, LV_ALIGN_LEFT_MID, LV_PART_MAIN | LV_STATE_DEFAULT);
                            lv_label_set_text(obj, "");
                        }
                        {
                            // WiFi Scanning Switch
                            lv_obj_t *obj = lv_switch_create(parent_obj);
                            objects.wi_fi_scanning_switch = obj;
                            lv_obj_set_pos(obj, 0, 0);
                            lv_obj_set_size(obj, 50, 25);
                            add_style_focused___switch(obj);
                        }
                    }
                }
                {
                    lv_obj_t *obj = lv_obj_create(parent_obj);
                    lv_obj_set_pos(obj, 0, 0);
                    lv_obj_set_size(obj, LV_PCT(100), LV_SIZE_CONTENT);
                    lv_obj_set_style_pad_left(obj, 0, LV_PART_MAIN | LV_STATE_DEFAULT);
                    lv_obj_set_style_pad_top(obj, 0, LV_PART_MAIN | LV_STATE_DEFAULT);
                    lv_obj_set_style_pad_right(obj, 0, LV_PART_MAIN | LV_STATE_DEFAULT);
                    lv_obj_set_style_pad_bottom(obj, 0, LV_PART_MAIN | LV_STATE_DEFAULT);
                    lv_obj_set_style_bg_opa(obj, 0, LV_PART_MAIN | LV_STATE_DEFAULT);
                    lv_obj_set_style_border_width(obj, 0, LV_PART_MAIN | LV_STATE_DEFAULT);
                    lv_obj_set_style_radius(obj, 0, LV_PART_MAIN | LV_STATE_DEFAULT);
                    {
                        lv_obj_t *parent_obj = obj;
                        {
                            lv_obj_t *obj = lv_label_create(parent_obj);
                            lv_obj_set_pos(obj, 0, 0);
                            lv_obj_set_size(obj, LV_SIZE_CONTENT, LV_SIZE_CONTENT);
                            lv_obj_set_style_align(obj, LV_ALIGN_LEFT_MID, LV_PART_MAIN | LV_STATE_DEFAULT);
                            lv_label_set_text_static(obj, "Scan Mode");
                        }
                        {
                            // Scan Mode Dropdown
                            lv_obj_t *obj = lv_dropdown_create(parent_obj);
                            objects.scan_mode_dropdown = obj;
                            lv_obj_set_pos(obj, 0, 0);
                            lv_obj_set_size(obj, LV_PCT(55), LV_SIZE_CONTENT);
                            lv_dropdown_set_options_static(obj, "Power Saver\nBalanced\nPerformance\nAlways-on");
                            lv_dropdown_set_selected(obj, 0);
                            add_style_focused___dropdown(obj);
                        }
                    }
                }
                {
                    lv_obj_t *obj = lv_label_create(parent_obj);
                    lv_obj_set_pos(obj, 0, 0);
                    lv_obj_set_size(obj, LV_SIZE_CONTENT, LV_SIZE_CONTENT);
                    lv_obj_set_style_text_decor(obj, LV_TEXT_DECOR_UNDERLINE, LV_PART_MAIN | LV_STATE_DEFAULT);
                    lv_obj_set_style_align(obj, LV_ALIGN_CENTER, LV_PART_MAIN | LV_STATE_DEFAULT);
                    lv_label_set_text_static(obj, "Debug Options");
                }
                {
                    lv_obj_t *obj = lv_obj_create(parent_obj);
                    lv_obj_set_pos(obj, 0, 0);
                    lv_obj_set_size(obj, LV_PCT(100), LV_SIZE_CONTENT);
                    lv_obj_set_style_pad_left(obj, 0, LV_PART_MAIN | LV_STATE_DEFAULT);
                    lv_obj_set_style_pad_top(obj, 0, LV_PART_MAIN | LV_STATE_DEFAULT);
                    lv_obj_set_style_pad_right(obj, 0, LV_PART_MAIN | LV_STATE_DEFAULT);
                    lv_obj_set_style_pad_bottom(obj, 0, LV_PART_MAIN | LV_STATE_DEFAULT);
                    lv_obj_set_style_bg_opa(obj, 0, LV_PART_MAIN | LV_STATE_DEFAULT);
                    lv_obj_set_style_border_width(obj, 0, LV_PART_MAIN | LV_STATE_DEFAULT);
                    lv_obj_set_style_radius(obj, 0, LV_PART_MAIN | LV_STATE_DEFAULT);
                    {
                        lv_obj_t *parent_obj = obj;
                        {
                            lv_obj_t *obj = lv_label_create(parent_obj);
                            lv_obj_set_pos(obj, 0, 0);
                            lv_obj_set_size(obj, LV_SIZE_CONTENT, LV_SIZE_CONTENT);
                            lv_obj_set_style_align(obj, LV_ALIGN_LEFT_MID, LV_PART_MAIN | LV_STATE_DEFAULT);
                            lv_label_set_text_static(obj, "Debug over Serial");
                        }
                        {
                            // Debug over Serial Switch
                            lv_obj_t *obj = lv_switch_create(parent_obj);
                            objects.debug_over_serial_switch = obj;
                            lv_obj_set_pos(obj, 0, 0);
                            lv_obj_set_size(obj, 50, 25);
                            add_style_focused___switch(obj);
                            lv_obj_set_style_align(obj, LV_ALIGN_RIGHT_MID, LV_PART_MAIN | LV_STATE_DEFAULT);
                        }
                    }
                }
                {
                    lv_obj_t *obj = lv_obj_create(parent_obj);
                    lv_obj_set_pos(obj, 0, 0);
                    lv_obj_set_size(obj, LV_PCT(100), LV_SIZE_CONTENT);
                    lv_obj_set_style_pad_left(obj, 0, LV_PART_MAIN | LV_STATE_DEFAULT);
                    lv_obj_set_style_pad_top(obj, 0, LV_PART_MAIN | LV_STATE_DEFAULT);
                    lv_obj_set_style_pad_right(obj, 0, LV_PART_MAIN | LV_STATE_DEFAULT);
                    lv_obj_set_style_pad_bottom(obj, 0, LV_PART_MAIN | LV_STATE_DEFAULT);
                    lv_obj_set_style_bg_opa(obj, 0, LV_PART_MAIN | LV_STATE_DEFAULT);
                    lv_obj_set_style_border_width(obj, 0, LV_PART_MAIN | LV_STATE_DEFAULT);
                    lv_obj_set_style_radius(obj, 0, LV_PART_MAIN | LV_STATE_DEFAULT);
                    {
                        lv_obj_t *parent_obj = obj;
                        {
                            lv_obj_t *obj = lv_label_create(parent_obj);
                            lv_obj_set_pos(obj, 0, 0);
                            lv_obj_set_size(obj, LV_SIZE_CONTENT, LV_SIZE_CONTENT);
                            lv_obj_set_style_align(obj, LV_ALIGN_LEFT_MID, LV_PART_MAIN | LV_STATE_DEFAULT);
                            lv_label_set_text_static(obj, "Debug Level");
                        }
                        {
                            // Debug Level Dropdown
                            lv_obj_t *obj = lv_dropdown_create(parent_obj);
                            objects.debug_level_dropdown = obj;
                            lv_obj_set_pos(obj, 0, 0);
                            lv_obj_set_size(obj, LV_PCT(55), LV_SIZE_CONTENT);
                            lv_dropdown_set_options_static(obj, "Info\nHigh\nRender\nScan\nPerf\nTeleplot");
                            lv_dropdown_set_selected(obj, 0);
                            add_style_focused___dropdown(obj);
                        }
                    }
                }
                {
                    lv_obj_t *obj = lv_obj_create(parent_obj);
                    lv_obj_set_pos(obj, 0, 0);
                    lv_obj_set_size(obj, LV_PCT(100), LV_SIZE_CONTENT);
                    lv_obj_set_style_pad_left(obj, 0, LV_PART_MAIN | LV_STATE_DEFAULT);
                    lv_obj_set_style_pad_top(obj, 0, LV_PART_MAIN | LV_STATE_DEFAULT);
                    lv_obj_set_style_pad_right(obj, 0, LV_PART_MAIN | LV_STATE_DEFAULT);
                    lv_obj_set_style_pad_bottom(obj, 0, LV_PART_MAIN | LV_STATE_DEFAULT);
                    lv_obj_set_style_bg_opa(obj, 0, LV_PART_MAIN | LV_STATE_DEFAULT);
                    lv_obj_set_style_border_width(obj, 0, LV_PART_MAIN | LV_STATE_DEFAULT);
                    lv_obj_set_style_radius(obj, 0, LV_PART_MAIN | LV_STATE_DEFAULT);
                    {
                        lv_obj_t *parent_obj = obj;
                        {
                            lv_obj_t *obj = lv_label_create(parent_obj);
                            lv_obj_set_pos(obj, 0, 0);
                            lv_obj_set_size(obj, LV_SIZE_CONTENT, LV_SIZE_CONTENT);
                            lv_obj_set_style_align(obj, LV_ALIGN_LEFT_MID, LV_PART_MAIN | LV_STATE_DEFAULT);
                            lv_label_set_text_static(obj, "Sleep with Serial");
                        }
                        {
                            // Sleep with Serial Switch
                            lv_obj_t *obj = lv_switch_create(parent_obj);
                            objects.sleep_with_serial_switch = obj;
                            lv_obj_set_pos(obj, 0, 0);
                            lv_obj_set_size(obj, 50, 25);
                            add_style_focused___switch(obj);
                            lv_obj_set_style_align(obj, LV_ALIGN_RIGHT_MID, LV_PART_MAIN | LV_STATE_DEFAULT);
                        }
                    }
                }
                {
                    lv_obj_t *obj = lv_obj_create(parent_obj);
                    lv_obj_set_pos(obj, 0, 0);
                    lv_obj_set_size(obj, LV_PCT(100), LV_SIZE_CONTENT);
                    lv_obj_set_style_pad_left(obj, 0, LV_PART_MAIN | LV_STATE_DEFAULT);
                    lv_obj_set_style_pad_top(obj, 0, LV_PART_MAIN | LV_STATE_DEFAULT);
                    lv_obj_set_style_pad_right(obj, 0, LV_PART_MAIN | LV_STATE_DEFAULT);
                    lv_obj_set_style_pad_bottom(obj, 0, LV_PART_MAIN | LV_STATE_DEFAULT);
                    lv_obj_set_style_bg_opa(obj, 0, LV_PART_MAIN | LV_STATE_DEFAULT);
                    lv_obj_set_style_border_width(obj, 0, LV_PART_MAIN | LV_STATE_DEFAULT);
                    lv_obj_set_style_radius(obj, 0, LV_PART_MAIN | LV_STATE_DEFAULT);
                    {
                        lv_obj_t *parent_obj = obj;
                        {
                            lv_obj_t *obj = lv_label_create(parent_obj);
                            lv_obj_set_pos(obj, 0, 0);
                            lv_obj_set_size(obj, LV_SIZE_CONTENT, LV_SIZE_CONTENT);
                            lv_obj_set_style_align(obj, LV_ALIGN_LEFT_MID, LV_PART_MAIN | LV_STATE_DEFAULT);
                            lv_label_set_text_static(obj, "Sleep with USB");
                        }
                        {
                            // Sleep with USB Switch
                            lv_obj_t *obj = lv_switch_create(parent_obj);
                            objects.sleep_with_usb_switch = obj;
                            lv_obj_set_pos(obj, 0, 0);
                            lv_obj_set_size(obj, 50, 25);
                            add_style_focused___switch(obj);
                            lv_obj_set_style_align(obj, LV_ALIGN_RIGHT_MID, LV_PART_MAIN | LV_STATE_DEFAULT);
                        }
                    }
                }
                {
                    lv_obj_t *obj = lv_obj_create(parent_obj);
                    lv_obj_set_pos(obj, 0, 0);
                    lv_obj_set_size(obj, LV_PCT(100), LV_SIZE_CONTENT);
                    lv_obj_set_style_pad_left(obj, 0, LV_PART_MAIN | LV_STATE_DEFAULT);
                    lv_obj_set_style_pad_top(obj, 0, LV_PART_MAIN | LV_STATE_DEFAULT);
                    lv_obj_set_style_pad_right(obj, 0, LV_PART_MAIN | LV_STATE_DEFAULT);
                    lv_obj_set_style_pad_bottom(obj, 0, LV_PART_MAIN | LV_STATE_DEFAULT);
                    lv_obj_set_style_bg_opa(obj, 0, LV_PART_MAIN | LV_STATE_DEFAULT);
                    lv_obj_set_style_border_width(obj, 0, LV_PART_MAIN | LV_STATE_DEFAULT);
                    lv_obj_set_style_radius(obj, 0, LV_PART_MAIN | LV_STATE_DEFAULT);
                    {
                        lv_obj_t *parent_obj = obj;
                        {
                            lv_obj_t *obj = lv_label_create(parent_obj);
                            lv_obj_set_pos(obj, 0, 0);
                            lv_obj_set_size(obj, LV_SIZE_CONTENT, LV_SIZE_CONTENT);
                            lv_obj_set_style_align(obj, LV_ALIGN_LEFT_MID, LV_PART_MAIN | LV_STATE_DEFAULT);
                            lv_label_set_text_static(obj, "Sleep while charging");
                        }
                        {
                            // Sleep while charging
                            lv_obj_t *obj = lv_switch_create(parent_obj);
                            objects.sleep_while_charging = obj;
                            lv_obj_set_pos(obj, 0, 0);
                            lv_obj_set_size(obj, 50, 25);
                            add_style_focused___switch(obj);
                            lv_obj_set_style_align(obj, LV_ALIGN_RIGHT_MID, LV_PART_MAIN | LV_STATE_DEFAULT);
                        }
                    }
                }
                {
                    lv_obj_t *obj = lv_obj_create(parent_obj);
                    lv_obj_set_pos(obj, 0, 0);
                    lv_obj_set_size(obj, LV_PCT(100), LV_SIZE_CONTENT);
                    lv_obj_set_style_pad_left(obj, 0, LV_PART_MAIN | LV_STATE_DEFAULT);
                    lv_obj_set_style_pad_top(obj, 0, LV_PART_MAIN | LV_STATE_DEFAULT);
                    lv_obj_set_style_pad_right(obj, 0, LV_PART_MAIN | LV_STATE_DEFAULT);
                    lv_obj_set_style_pad_bottom(obj, 0, LV_PART_MAIN | LV_STATE_DEFAULT);
                    lv_obj_set_style_bg_opa(obj, 0, LV_PART_MAIN | LV_STATE_DEFAULT);
                    lv_obj_set_style_border_width(obj, 0, LV_PART_MAIN | LV_STATE_DEFAULT);
                    lv_obj_set_style_radius(obj, 0, LV_PART_MAIN | LV_STATE_DEFAULT);
                    {
                        lv_obj_t *parent_obj = obj;
                        {
                            // Debug screen label
                            lv_obj_t *obj = lv_label_create(parent_obj);
                            objects.debug_screen_label = obj;
                            lv_obj_set_pos(obj, 0, 0);
                            lv_obj_set_size(obj, LV_SIZE_CONTENT, LV_SIZE_CONTENT);
                            lv_obj_set_style_align(obj, LV_ALIGN_LEFT_MID, LV_PART_MAIN | LV_STATE_DEFAULT);
                            lv_label_set_text_static(obj, "Debug screen");
                        }
                        {
                            // Debug screen button
                            lv_obj_t *obj = lv_button_create(parent_obj);
                            objects.debug_screen_button = obj;
                            lv_obj_set_pos(obj, 0, 0);
                            lv_obj_set_size(obj, LV_SIZE_CONTENT, LV_SIZE_CONTENT);
                            lv_obj_add_event_cb(obj, event_handler_cb_settings_debug_screen_button, LV_EVENT_ALL, flowState);
                            lv_obj_add_flag(obj, LV_OBJ_FLAG_OVERFLOW_VISIBLE);
                            add_style_focused___button(obj);
                            {
                                lv_obj_t *parent_obj = obj;
                                {
                                    lv_obj_t *obj = lv_label_create(parent_obj);
                                    objects.obj33 = obj;
                                    lv_obj_set_pos(obj, 0, 0);
                                    lv_obj_set_size(obj, LV_SIZE_CONTENT, LV_SIZE_CONTENT);
                                    lv_obj_set_style_align(obj, LV_ALIGN_CENTER, LV_PART_MAIN | LV_STATE_DEFAULT);
                                    lv_label_set_text(obj, "");
                                }
                            }
                        }
                    }
                }
                {
                    lv_obj_t *obj = lv_obj_create(parent_obj);
                    lv_obj_set_pos(obj, 0, 0);
                    lv_obj_set_size(obj, LV_PCT(100), LV_SIZE_CONTENT);
                    lv_obj_set_style_pad_left(obj, 0, LV_PART_MAIN | LV_STATE_DEFAULT);
                    lv_obj_set_style_pad_top(obj, 0, LV_PART_MAIN | LV_STATE_DEFAULT);
                    lv_obj_set_style_pad_right(obj, 0, LV_PART_MAIN | LV_STATE_DEFAULT);
                    lv_obj_set_style_pad_bottom(obj, 0, LV_PART_MAIN | LV_STATE_DEFAULT);
                    lv_obj_set_style_bg_opa(obj, 0, LV_PART_MAIN | LV_STATE_DEFAULT);
                    lv_obj_set_style_border_width(obj, 0, LV_PART_MAIN | LV_STATE_DEFAULT);
                    lv_obj_set_style_radius(obj, 0, LV_PART_MAIN | LV_STATE_DEFAULT);
                    {
                        lv_obj_t *parent_obj = obj;
                        {
                            // Sleep timer label
                            lv_obj_t *obj = lv_label_create(parent_obj);
                            objects.sleep_timer_label = obj;
                            lv_obj_set_pos(obj, 0, 0);
                            lv_obj_set_size(obj, LV_SIZE_CONTENT, LV_SIZE_CONTENT);
                            lv_obj_set_style_align(obj, LV_ALIGN_LEFT_MID, LV_PART_MAIN | LV_STATE_DEFAULT);
                            lv_label_set_text_static(obj, "Will not sleep");
                        }
                        {
                            // Sleep Button
                            lv_obj_t *obj = lv_button_create(parent_obj);
                            objects.sleep_button = obj;
                            lv_obj_set_pos(obj, 0, 0);
                            lv_obj_set_size(obj, LV_SIZE_CONTENT, LV_SIZE_CONTENT);
                            lv_obj_add_flag(obj, LV_OBJ_FLAG_OVERFLOW_VISIBLE);
                            add_style_focused___button(obj);
                            {
                                lv_obj_t *parent_obj = obj;
                                {
                                    lv_obj_t *obj = lv_label_create(parent_obj);
                                    objects.obj34 = obj;
                                    lv_obj_set_pos(obj, 0, 0);
                                    lv_obj_set_size(obj, LV_SIZE_CONTENT, LV_SIZE_CONTENT);
                                    lv_obj_set_style_align(obj, LV_ALIGN_CENTER, LV_PART_MAIN | LV_STATE_DEFAULT);
                                    lv_label_set_text(obj, "");
                                }
                            }
                        }
                    }
                }
                {
                    lv_obj_t *obj = lv_obj_create(parent_obj);
                    lv_obj_set_pos(obj, 0, 0);
                    lv_obj_set_size(obj, LV_PCT(100), LV_SIZE_CONTENT);
                    lv_obj_set_style_pad_left(obj, 0, LV_PART_MAIN | LV_STATE_DEFAULT);
                    lv_obj_set_style_pad_top(obj, 0, LV_PART_MAIN | LV_STATE_DEFAULT);
                    lv_obj_set_style_pad_right(obj, 0, LV_PART_MAIN | LV_STATE_DEFAULT);
                    lv_obj_set_style_pad_bottom(obj, 0, LV_PART_MAIN | LV_STATE_DEFAULT);
                    lv_obj_set_style_bg_opa(obj, 0, LV_PART_MAIN | LV_STATE_DEFAULT);
                    lv_obj_set_style_border_width(obj, 0, LV_PART_MAIN | LV_STATE_DEFAULT);
                    lv_obj_set_style_radius(obj, 0, LV_PART_MAIN | LV_STATE_DEFAULT);
                    {
                        lv_obj_t *parent_obj = obj;
                        {
                            lv_obj_t *obj = lv_label_create(parent_obj);
                            lv_obj_set_pos(obj, 0, 0);
                            lv_obj_set_size(obj, LV_SIZE_CONTENT, LV_SIZE_CONTENT);
                            lv_obj_set_style_align(obj, LV_ALIGN_LEFT_MID, LV_PART_MAIN | LV_STATE_DEFAULT);
                            lv_label_set_text_static(obj, "Reboot device");
                        }
                        {
                            // Reboot Button
                            lv_obj_t *obj = lv_button_create(parent_obj);
                            objects.reboot_button = obj;
                            lv_obj_set_pos(obj, 0, 0);
                            lv_obj_set_size(obj, LV_SIZE_CONTENT, LV_SIZE_CONTENT);
                            lv_obj_add_flag(obj, LV_OBJ_FLAG_OVERFLOW_VISIBLE);
                            add_style_focused___button(obj);
                            {
                                lv_obj_t *parent_obj = obj;
                                {
                                    lv_obj_t *obj = lv_label_create(parent_obj);
                                    objects.obj35 = obj;
                                    lv_obj_set_pos(obj, 0, 0);
                                    lv_obj_set_size(obj, LV_SIZE_CONTENT, LV_SIZE_CONTENT);
                                    lv_obj_set_style_align(obj, LV_ALIGN_CENTER, LV_PART_MAIN | LV_STATE_DEFAULT);
                                    lv_label_set_text(obj, "");
                                }
                            }
                        }
                    }
                }
                {
                    lv_obj_t *obj = lv_obj_create(parent_obj);
                    lv_obj_set_pos(obj, 0, 0);
                    lv_obj_set_size(obj, LV_PCT(100), LV_SIZE_CONTENT);
                    lv_obj_set_style_pad_left(obj, 0, LV_PART_MAIN | LV_STATE_DEFAULT);
                    lv_obj_set_style_pad_top(obj, 0, LV_PART_MAIN | LV_STATE_DEFAULT);
                    lv_obj_set_style_pad_right(obj, 0, LV_PART_MAIN | LV_STATE_DEFAULT);
                    lv_obj_set_style_pad_bottom(obj, 0, LV_PART_MAIN | LV_STATE_DEFAULT);
                    lv_obj_set_style_bg_opa(obj, 0, LV_PART_MAIN | LV_STATE_DEFAULT);
                    lv_obj_set_style_border_width(obj, 0, LV_PART_MAIN | LV_STATE_DEFAULT);
                    lv_obj_set_style_radius(obj, 0, LV_PART_MAIN | LV_STATE_DEFAULT);
                    {
                        lv_obj_t *parent_obj = obj;
                        {
                            lv_obj_t *obj = lv_label_create(parent_obj);
                            lv_obj_set_pos(obj, 0, 0);
                            lv_obj_set_size(obj, LV_SIZE_CONTENT, LV_SIZE_CONTENT);
                            lv_obj_set_style_align(obj, LV_ALIGN_LEFT_MID, LV_PART_MAIN | LV_STATE_DEFAULT);
                            lv_label_set_text_static(obj, "Shipping mode");
                        }
                        {
                            // Shipping Mode Button
                            lv_obj_t *obj = lv_button_create(parent_obj);
                            objects.shipping_mode_button = obj;
                            lv_obj_set_pos(obj, 0, 0);
                            lv_obj_set_size(obj, LV_SIZE_CONTENT, LV_SIZE_CONTENT);
                            lv_obj_add_flag(obj, LV_OBJ_FLAG_OVERFLOW_VISIBLE);
                            add_style_focused___button(obj);
                            {
                                lv_obj_t *parent_obj = obj;
                                {
                                    lv_obj_t *obj = lv_label_create(parent_obj);
                                    objects.obj36 = obj;
                                    lv_obj_set_pos(obj, 0, 0);
                                    lv_obj_set_size(obj, LV_SIZE_CONTENT, LV_SIZE_CONTENT);
                                    lv_obj_set_style_align(obj, LV_ALIGN_CENTER, LV_PART_MAIN | LV_STATE_DEFAULT);
                                    lv_label_set_text(obj, "");
                                }
                            }
                        }
                    }
                }
                {
                    lv_obj_t *obj = lv_obj_create(parent_obj);
                    lv_obj_set_pos(obj, 0, 0);
                    lv_obj_set_size(obj, LV_PCT(100), LV_SIZE_CONTENT);
                    lv_obj_set_style_pad_left(obj, 0, LV_PART_MAIN | LV_STATE_DEFAULT);
                    lv_obj_set_style_pad_top(obj, 0, LV_PART_MAIN | LV_STATE_DEFAULT);
                    lv_obj_set_style_pad_right(obj, 0, LV_PART_MAIN | LV_STATE_DEFAULT);
                    lv_obj_set_style_pad_bottom(obj, 0, LV_PART_MAIN | LV_STATE_DEFAULT);
                    lv_obj_set_style_bg_opa(obj, 0, LV_PART_MAIN | LV_STATE_DEFAULT);
                    lv_obj_set_style_border_width(obj, 0, LV_PART_MAIN | LV_STATE_DEFAULT);
                    lv_obj_set_style_radius(obj, 0, LV_PART_MAIN | LV_STATE_DEFAULT);
                    {
                        lv_obj_t *parent_obj = obj;
                        {
                            lv_obj_t *obj = lv_label_create(parent_obj);
                            lv_obj_set_pos(obj, 0, 0);
                            lv_obj_set_size(obj, LV_SIZE_CONTENT, LV_SIZE_CONTENT);
                            lv_obj_set_style_align(obj, LV_ALIGN_LEFT_MID, LV_PART_MAIN | LV_STATE_DEFAULT);
                            lv_label_set_text_static(obj, "Restart tutorial");
                        }
                        {
                            // Restart Tutorial Button
                            lv_obj_t *obj = lv_button_create(parent_obj);
                            objects.restart_tutorial_button = obj;
                            lv_obj_set_pos(obj, 0, 0);
                            lv_obj_set_size(obj, LV_SIZE_CONTENT, LV_SIZE_CONTENT);
                            lv_obj_add_event_cb(obj, event_handler_cb_settings_restart_tutorial_button, LV_EVENT_ALL, flowState);
                            lv_obj_add_flag(obj, LV_OBJ_FLAG_OVERFLOW_VISIBLE);
                            add_style_focused___button(obj);
                            {
                                lv_obj_t *parent_obj = obj;
                                {
                                    lv_obj_t *obj = lv_label_create(parent_obj);
                                    objects.obj37 = obj;
                                    lv_obj_set_pos(obj, 0, 0);
                                    lv_obj_set_size(obj, LV_SIZE_CONTENT, LV_SIZE_CONTENT);
                                    lv_obj_set_style_align(obj, LV_ALIGN_CENTER, LV_PART_MAIN | LV_STATE_DEFAULT);
                                    lv_label_set_text(obj, "");
                                }
                            }
                        }
                    }
                }
            }
        }
    }
    
    tick_screen_settings();
}

void tick_screen_settings() {
    void *flowState = getFlowState(0, 3);
    (void)flowState;
    tick_user_widget_top_bar(getFlowState(flowState, 0), 21);
    {
        const char *new_val = evalTextProperty(flowState, 25, 3, "Failed to evaluate Text in Label widget");
        const char *cur_val = lv_label_get_text(objects.obj29);
        if (strcmp(new_val, cur_val) != 0) {
            tick_value_change_obj = objects.obj29;
            lv_label_set_text(objects.obj29, new_val);
            tick_value_change_obj = NULL;
        }
    }
    {
        const char *new_val = evalTextProperty(flowState, 28, 3, "Failed to evaluate Text in Label widget");
        const char *cur_val = lv_label_get_text(objects.obj30);
        if (strcmp(new_val, cur_val) != 0) {
            tick_value_change_obj = objects.obj30;
            lv_label_set_text(objects.obj30, new_val);
            tick_value_change_obj = NULL;
        }
    }
    {
        const char *new_val = evalTextProperty(flowState, 31, 3, "Failed to evaluate Text in Label widget");
        const char *cur_val = lv_label_get_text(objects.obj31);
        if (strcmp(new_val, cur_val) != 0) {
            tick_value_change_obj = objects.obj31;
            lv_label_set_text(objects.obj31, new_val);
            tick_value_change_obj = NULL;
        }
    }
    {
        const char *new_val = evalTextProperty(flowState, 34, 3, "Failed to evaluate Text in Label widget");
        const char *cur_val = lv_label_get_text(objects.obj32);
        if (strcmp(new_val, cur_val) != 0) {
            tick_value_change_obj = objects.obj32;
            lv_label_set_text(objects.obj32, new_val);
            tick_value_change_obj = NULL;
        }
    }
    {
        const char *new_val = evalTextProperty(flowState, 58, 3, "Failed to evaluate Text in Label widget");
        const char *cur_val = lv_label_get_text(objects.obj33);
        if (strcmp(new_val, cur_val) != 0) {
            tick_value_change_obj = objects.obj33;
            lv_label_set_text(objects.obj33, new_val);
            tick_value_change_obj = NULL;
        }
    }
    {
        const char *new_val = evalTextProperty(flowState, 62, 3, "Failed to evaluate Text in Label widget");
        const char *cur_val = lv_label_get_text(objects.obj34);
        if (strcmp(new_val, cur_val) != 0) {
            tick_value_change_obj = objects.obj34;
            lv_label_set_text(objects.obj34, new_val);
            tick_value_change_obj = NULL;
        }
    }
    {
        const char *new_val = evalTextProperty(flowState, 66, 3, "Failed to evaluate Text in Label widget");
        const char *cur_val = lv_label_get_text(objects.obj35);
        if (strcmp(new_val, cur_val) != 0) {
            tick_value_change_obj = objects.obj35;
            lv_label_set_text(objects.obj35, new_val);
            tick_value_change_obj = NULL;
        }
    }
    {
        const char *new_val = evalTextProperty(flowState, 70, 3, "Failed to evaluate Text in Label widget");
        const char *cur_val = lv_label_get_text(objects.obj36);
        if (strcmp(new_val, cur_val) != 0) {
            tick_value_change_obj = objects.obj36;
            lv_label_set_text(objects.obj36, new_val);
            tick_value_change_obj = NULL;
        }
    }
    {
        const char *new_val = evalTextProperty(flowState, 74, 3, "Failed to evaluate Text in Label widget");
        const char *cur_val = lv_label_get_text(objects.obj37);
        if (strcmp(new_val, cur_val) != 0) {
            tick_value_change_obj = objects.obj37;
            lv_label_set_text(objects.obj37, new_val);
            tick_value_change_obj = NULL;
        }
    }
}
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
