Cade-Bray/Helgatchi/Software/Helgatchi-Firmware/src/UI/vars.h

#ifndef EEZ_LVGL_UI_VARS_H
#define EEZ_LVGL_UI_VARS_H

#include <stdint.h>
#include <stdbool.h>

#ifdef __cplusplus
extern "C" {
#endif

// enum declarations

// Flow global variables

enum FlowGlobalVariables {
    FLOW_GLOBAL_VARIABLE_BATTERY_STATUS = 0,
    FLOW_GLOBAL_VARIABLE_STATUS_ICONS = 1
};

// Native global variables

#ifdef __cplusplus
}
#endif

#endif /*EEZ_LVGL_UI_VARS_H*/
